amrikarisma/stm32f407xxx-mega-layout/firmware/speeduino/202501/speeduino.ini

;-------------------------------------------------------------------------------
#unset enablehardware_test

[MegaTune]
   MTversion      = 2.25

   queryCommand   = "Q"
   signature      = "speeduino 202501"
   versionInfo    = "S" ;This info is what is displayed to user

[TunerStudio]
   iniSpecVersion = 3.64

;-------------------------------------------------------------------------------

[SettingGroups]
   ; the referenceName will over-ride previous, so if you are creating a
   ; settingGroup with a reference name of lambdaSensor, it will replace the
   ; setting group defined in the settingGroups.xml of the TunerStudio config
   ; folder. If is is an undefined referenceName, it will be added.
   ; keyword    =  referenceName,  DisplayName

    ;settingGroup = boostUnits, "Boost table units"
    ;settingOption = DEFAULT, "kPa"
    ;settingOption = BOOSTPSI, "PSI"

    settingGroup = pressure_units, "Pressure Display"
    settingOption = DEFAULT, "PSI"
    settingOption = pressure_bar, "BAR"

    settingGroup = enablehardware_test, "Enable Hardware Test Page"

    settingGroup = resetcontrol_group, "Reset Control Features"
    settingOption = resetcontrol_standard, "Basic Options Only"
    settingOption = resetcontrol_adv, "Advanced Features (16u2 Firmware Update Required)"

    settingGroup  = mcu, "Controller in use"
    settingOption = DEFAULT, "Arduino Mega 2560"
    settingOption = mcu_teensy, "Teensy"
    settingOption = mcu_stm32, "STM32"

    settingGroup = COMMS_COMPAT_GROUP, "Serial Mode"
    settingOption = COMMS_COMPAT, "Compatibility Mode"
    settingOption = DEFAULT, "Normal"

    settingGroup = COMMS_MSDROID_COMPAT, "msDroid Compatibility-ONLY enable on Android"
    settingOption = MSDROID_COMPAT, "Enable"
    settingOption = DEFAULT, "Disable"

[PcVariables]
   ; valid types: boolean, double, int, list
   ;
   ; no offset as they are local variables.
   ; entry format the same as Constants, except there is no offset.
   ; arrays are not yet supported.
   ; name = class,  type,    shape,  units,       scale, translate,    lo,      hi, digits
   ; name = type, min, max;
   ;
   ; type List: value will be index.
    tsCanId          = bits,     U08,   [0:3], "CAN ID 0", "CAN ID 1", "CAN ID 2", "CAN ID 3", "CAN ID 4", "CAN ID 5", "CAN ID 6", "CAN ID 7", "CAN ID 8", "CAN ID 9", "CAN ID 10","CAN ID 11","CAN ID 12","CAN ID 13","CAN ID 14","INVALID"
    rpmhigh = scalar,   U16,    "rpm", 1, 0, 0, 30000, 0
    rpmwarn = scalar,   U16,    "rpm", 1, 0, 0, 30000, 0
    rpmdang = scalar,   U16,    "rpm", 1, 0, 0, 30000, 0
    maphigh = scalar,   U16,    "kPa", 1, 0, 0, 30000, 0
    mapwarn = scalar,   U16,    "kPa", 1, 0, 0, 30000, 0
    mapdang = scalar,   U16,    "kPa", 1, 0, 0, 30000, 0
    batlow  = scalar,   U08,    "Volts",  .1, 0, 0, 25.5,   1
    bathigh = scalar,   U08,    "Volts",  .1, 0, 0, 25.5,   1

#if LAMBDA
    wueAFR = array, S16,  [10], "Lambda", { 0.1 / stoich }, 0.000, -0.300, 0.300, 3
#else
    wueAFR = array, S16,  [10], "AFR", 0.1,   0.0, -4.0, 4.0, 1
#endif
    wueRecommended = array, U08,  [10], "%", 1.0,  0.0, 100, 255.0, 0

    idleUnits = bits,   U08,    [0:2], "None", "On/Off", "Duty Cycle", "Duty Cycle", "Steps", "Steps"

    boardFuelOutputs  = array,   U08,   [128],   " ", 1.0, 0, 0, 255, 0, noMsqSave
    boardIgnOutputs   = array,   U08,   [128],   " ", 1.0, 0, 0, 255, 0, noMsqSave
    boardHasRTC       = array,   U08,   [128],   " ", 1.0, 0, 0, 255, 0, noMsqSave

    ;These are used for padding out bits variables
    #define invalid_x8      = "INVALID", "INVALID", "INVALID", "INVALID", "INVALID", "INVALID", "INVALID", "INVALID"
    #define invalid_x16     = $invalid_x8,  $invalid_x8
    #define invalid_x24     = $invalid_x16, $invalid_x8
    #define invalid_x32     = $invalid_x16, $invalid_x16
    #define invalid_x64     = $invalid_x32, $invalid_x32
    #define invalid_x128    = $invalid_x64, $invalid_x64
    #define invalid_x256    = $invalid_x128, $invalid_x128
    #define invalid_x512    = $invalid_x256, $invalid_x256
    #define invalid_x1024   = $invalid_x512, $invalid_x512
    #define invalid_x2048   = $invalid_x1024, $invalid_x1024
    #define invalid_x4096   = $invalid_x2048, $invalid_x2048
    #define invalid_x8192   = $invalid_x4096, $invalid_x4096
    #define invalid_x16384  = $invalid_x8192, $invalid_x8192
    #define invalid_x32768  = $invalid_x16384, $invalid_x16384

    #define loadSourceNames = "MAP", "TPS", "IMAP/EMAP", "INVALID",   "INVALID", "INVALID", "INVALID", "INVALID"
    #define loadSourceUnits = "kPa",           "% TPS",   "%",         "INVALID", "INVALID", "INVALID", "INVALID", "INVALID"
    algorithmNames          = bits,    U08,   [0:2], $loadSourceNames
    algorithmUnits          = bits,    U08,   [0:2], "kPa",           "% TPS",   "%",         "% TPS", "INVALID", "INVALID", "INVALID", "INVALID"
    algorithmLimits         = array,   U16,   [8],   "", 1.0, 0, 0, 511, 0, noMsqSave
    fuel2SwitchUnits        = bits,    U08,   [0:2], "rpm", "kPa",          "% TPS",   "%",         "% TPS", "INVALID", "INVALID", "INVALID"

    ;All definitions of split fullStatus should keep 32 options
    #define fullStatus_def_1= "seconds", "status bits", "Engine status", "syncLossCounter", "MAP (Kpa)", "INVALID", "IAT / MAT", "coolant",  "batCorrection", "battery voltage x10", "O2", "egoCorrection", "iatCorrection", "wueCorrection", "RPM", "INVALID", "AEamount/2", "GammaE", "INVALID", "VE1", "VE2", "AFR Target", "TPS DOT", "INVALID", "Advance", "TPS", "loopsPerSecond", "INVALID", "free RAM", "INVALID", "boostTarget/2", "Boost duty"
    #define fullStatus_def_2= "spark bits", "RPM DOT", "INVALID", "ethanolPct", "flexCorrection", "flexIgnCorrection", "idle Load", "testOutputs", "O2_2", "baro", "Aux in 0", "INVALID", "Aux in 1", "INVALID", "Aux in 2", "INVALID", "Aux in 3", "INVALID", "Aux in 4", "INVALID", "Aux in 5", "INVALID", "Aux in 6", "INVALID", "Aux in 7", "INVALID", "Aux in 8", "INVALID", "Aux in 9", "INVALID", "Aux in 10", "INVALID"
    #define fullStatus_def_3= "Aux in 11", "INVALID", "Aux in 12", "INVALID", "Aux in 13", "INVALID", "Aux in 14", "INVALID", "Aux in 15", "INVALID", "TPS ADC", "Error code", "Pulsewidth 1", "INVALID", "Pulsewidth 2", "INVALID", "Pulsewidth 3", "INVALID", "Pulsewidth 4", "INVALID", "status bits 3", "engineProtectStatus", "Fuel load", "INVALID", "Ignition load", "INVALID", "dwell", "INVALID", "idle C.L. target", "MAP DOT", "INVALID", "VVT1 Angle"
    #define fullStatus_def_4= "INVALID", "VVT1 Target", "VVT1 duty", "flexBoostCorrection", "INVALID", "baro correction", "Current VE", "ASE Value", "vss", "INVALID", "Gear", "Fuel Pressure", "Oil Pressure", "WMI duty", "WMI empty", "VVT2 angle", "INVALID", "VVT2 target", "VVT2 duty", "outputs status", "Fuel temp", "Fuel temp correction", "Advance 1", "Advance 2", "SD status", "EMAP", "INVALID", "Fan duty", "airConStatus", "INVALID", "INVALID"
    #define fullStatus_def_5= $invalid_x32
    #define fullStatus_def_6= $invalid_x32
    #define fullStatus_def_7= $invalid_x32
    ;Rules start at index 240
    #define fullStatus_def_8= "INVALID", "INVALID", "INVALID", "INVALID", "INVALID", "INVALID", "INVALID", "INVALID", "INVALID", "INVALID", "INVALID", "INVALID", "INVALID", "INVALID", "INVALID", "INVALID", "running seconds x10", "Rule 1", "Rule 2", "Rule 3", "Rule 4", "Rule 5", "Rule 6", "Rule 7", "Rule 8", "INVALID", "INVALID", "INVALID", "INVALID", "INVALID", "INVALID", "INVALID", "INVALID"
    #define fullStatus_def  = $fullStatus_def_1, $fullStatus_def_2, $fullStatus_def_3, $fullStatus_def_4, $fullStatus_def_5, $fullStatus_def_6, $fullStatus_def_7, $fullStatus_def_8

    #define pinLayouts      = "INVALID", "Speeduino v0.2", "Speeduino v0.3", "Speeduino v0.4", "INVALID", "INVALID", "01-05 MX5 PNP", "INVALID", "96-97 MX5 PNP", "NA6 MX5 PNP", "Turtana PCB", "INVALID", "INVALID", "INVALID", "INVALID", "INVALID", "INVALID", "INVALID", "INVALID", "INVALID", "Plazomat I/O 0.1", "INVALID", "INVALID", "INVALID", "INVALID", "INVALID", "INVALID", "INVALID", "INVALID", "INVALID", "Daz V6 Shield 0.1", "BMW PnP", "INVALID", "INVALID", "INVALID", "INVALID", "INVALID", "INVALID", "INVALID", "INVALID", "NO2C", "UA4C", "BlitzboxBL49sp", "INVALID", "INVALID", "DIY-EFI CORE4 v1.0", "INVALID", "INVALID", "INVALID", "INVALID", "dvjcodec Teensy RevA", "dvjcodec Teensy RevB", "INVALID", "JUICEBOX", "INVALID", "Drop Bear", "INVALID", "INVALID", "INVALID", "INVALID", "Black STM32F407VET6 V0.1", "INVALID", "INVALID", "INVALID", "Mazduino Compact", $invalid_x128, $invalid_x64

    boostTableLabels    = bits,    U08,   [0:1], "Duty Cycle %", "kPa"
    boostByGearLabels   = bits,    U08,   [0:1], "", "%", "Limit", ""
    prgm_out_selection  = bits,    U08,   [0:2], "1", "2", "3", "4", "5", "6", "7", "8"

    fuelLoadMax     = scalar, U08, "", 1, 0, 0, 511, 0
    ignLoadMax      = scalar, U08, "", 1, 0, 0, 511, 0
    fuel2LoadMax    = scalar, U08, "", 1, 0, 0, 511, 0
    ign2LoadMax     = scalar, U08, "", 1, 0, 0, 511, 0
    AUXin00Alias    = string, ASCII, 20
    AUXin01Alias    = string, ASCII, 20 
    AUXin02Alias    = string, ASCII, 20 
    AUXin03Alias    = string, ASCII, 20 
    AUXin04Alias    = string, ASCII, 20 
    AUXin05Alias    = string, ASCII, 20 
    AUXin06Alias    = string, ASCII, 20 
    AUXin07Alias    = string, ASCII, 20 
    AUXin08Alias    = string, ASCII, 20 
    AUXin09Alias    = string, ASCII, 20 
    AUXin10Alias    = string, ASCII, 20 
    AUXin11Alias    = string, ASCII, 20 
    AUXin12Alias    = string, ASCII, 20 
    AUXin13Alias    = string, ASCII, 20 
    AUXin14Alias    = string, ASCII, 20 
    AUXin15Alias    = string, ASCII, 20

    prgm_out00Alias  = string, ASCII, 20
    prgm_out01Alias  = string, ASCII, 20 
    prgm_out02Alias  = string, ASCII, 20 
    prgm_out03Alias  = string, ASCII, 20 
    prgm_out04Alias  = string, ASCII, 20 
    prgm_out05Alias  = string, ASCII, 20 
    prgm_out06Alias  = string, ASCII, 20 
    prgm_out07Alias  = string, ASCII, 20 

    ;Define aliases for all the triggers. Naming pattern matches that used in decoders.ino
    #define trigger_missingTooth        = 0
    #define trigger_BasicDistributor    = 1
    #define trigger_DualWheel           = 2
    #define trigger_GM7X                = 3
    #define trigger_4G63                = 4
    #define trigger_24X                 = 5
    #define trigger_Jeep2000            = 6
    #define trigger_Audi135             = 7
    #define trigger_HondaD17            = 8
    #define trigger_Miata9905           = 9
    #define trigger_MazdaAU             = 10
    #define trigger_non360              = 11
    #define trigger_Nissan360           = 12
    #define trigger_Subaru67            = 13
    #define trigger_Daihatsu            = 14
    #define trigger_Harley              = 15
    #define trigger_ThirtySixMinus222   = 16
    #define trigger_ThirtySixMinus21    = 17
    #define trigger_420a                = 18
    #define trigger_Webber              = 19
    #define trigger_FordST170           = 20
    #define trigger_DRZ400              = 21
    #define trigger_NGC                 = 22
    #define trigger_VMAX                = 23
    #define trigger_renix               = 24
    #define trigger_Rover				        = 25
    #define trigger_K6A  				        = 26
    #define trigger_HondaJ32            = 27

[Constants]

   ;----------------------------------------------------------------------------
   ; Constants Definition
   ; --------------------
   ;
   ; Scalar Values
   ; -------------
   ; The scaling and translation values are used as follows:
   ;    msValue   = userValue / scale - translate
   ;    userValue = (msValue + translate) * scale
   ;
   ;
   ; Temperatures are fine, check out the Fielding IAC example (fastIdleT).
   ;
   ; Array Values
   ; ------------
   ; Arrays are specified just like scalars, except that they have a "shape"
   ; entry in the fourth parameter.  The shape allows you to define lists or
   ; tables, for example [8] defines a list with eight values and [2x4] defines
   ; a table with eight values (two rows and four columns).  Tables may be
   ; stored in either "X-" or "Y-order."  X-order means that memory is laid
   ; out like.
   ;
   ;     [x1,y1] [x2,y1]...[xn,y1] [x1,y2]...
   ;
   ; Y-order would be
   ;
   ;     [x1,y1] [x1,y2]...[x1,yn] [x2,y1]...
   ;
   ; To use the TableEditor, you must define two lists and a table, and
   ; the lengths of the lists must correspond to the shape of the table.
   ;
   ; Bit Fields
   ; ----------
   ; Bits are numbered 0-7, the rightmost being bit zero.  The basic
   ; data word that stores bit fields must be unsigned.
   ;
   ; You need NOT supply the correct number of labels matching the
   ; number of bits you've specified (one bit requires 2 values, two
   ; bits requires 4 values and so on).  If you neglect to supply enough
   ; labels, they will be synthesised using the sequence "1", "2" and so
   ; on based upon their position in the sequence (the cltType and matType
   ; will end up with identical lists).
   ;
   ; If you specify a label as "INVALID" (all upper case), then it will
   ; not be displayed in the combo box, so you can leave out values that
   ; make no sense.
   ;
   ;----------------------------------------------------------------------------

    endianness          = little
    nPages              = 15
    pageSize            = 128,   288,     288,    128,     288,    128,    240,     384,    192,    192,    288,    192,    128,    288,    256

    ; New commands
    pageIdentifier      = "\$tsCanId\x01", "\$tsCanId\x02", "\$tsCanId\x03", "\$tsCanId\x04", "\$tsCanId\x05", "\$tsCanId\x06", "\$tsCanId\x07", "\$tsCanId\x08", "\$tsCanId\x09", "\$tsCanId\x0A", "\$tsCanId\x0B", "\$tsCanId\x0C", "\$tsCanId\x0D", "\$tsCanId\x0E", "\$tsCanId\x0F"
    pageReadCommand     = "p%2i%2o%2c", "p%2i%2o%2c", "p%2i%2o%2c", "p%2i%2o%2c", "p%2i%2o%2c", "p%2i%2o%2c", "p%2i%2o%2c", "p%2i%2o%2c", "p%2i%2o%2c", "p%2i%2o%2c", "p%2i%2o%2c", "p%2i%2o%2c", "p%2i%2o%2c", "p%2i%2o%2c", "p%2i%2o%2c"
    pageValueWrite      = "M%2i%2o%2c%v", "M%2i%2o%2c%v", "M%2i%2o%2c%v", "M%2i%2o%2c%v", "M%2i%2o%2c%v", "M%2i%2o%2c%v", "M%2i%2o%2c%v", "M%2i%2o%2c%v", "M%2i%2o%2c%v", "M%2i%2o%2c%v", "M%2i%2o%2c%v", "M%2i%2o%2c%v", "M%2i%2o%2c%v", "M%2i%2o%2c%v", "M%2i%2o%2c%v"
    pageChunkWrite      = "M%2i%2o%2c%v", "M%2i%2o%2c%v", "M%2i%2o%2c%v", "M%2i%2o%2c%v", "M%2i%2o%2c%v", "M%2i%2o%2c%v", "M%2i%2o%2c%v", "M%2i%2o%2c%v", "M%2i%2o%2c%v", "M%2i%2o%2c%v", "M%2i%2o%2c%v", "M%2i%2o%2c%v", "M%2i%2o%2c%v", "M%2i%2o%2c%v", "M%2i%2o%2c%v"
    crc32CheckCommand   = "d%2i", "d%2i", "d%2i", "d%2i", "d%2i", "d%2i", "d%2i", "d%2i", "d%2i", "d%2i", "d%2i", "d%2i", "d%2i", "d%2i", "d%2i"
#if COMMS_COMPAT
    ;Comms compat mode uses a different burn command in order to slow down the EEPROM burn rate
    burnCommand         = "B%2i", "B%2i", "B%2i", "B%2i", "B%2i", "B%2i", "B%2i", "B%2i", "B%2i", "B%2i", "B%2i", "B%2i", "B%2i", "B%2i", "B%2i"
#else
    burnCommand         = "b%2i", "b%2i", "b%2i", "b%2i", "b%2i", "b%2i", "b%2i", "b%2i", "b%2i", "b%2i", "b%2i", "b%2i", "b%2i", "b%2i", "b%2i"
#endif


#if mcu_stm32
    blockingFactor = 121
#else
    blockingFactor = 251 ; Serial buffer is 257 bytes and there are 6 bytes of overhead (2 for the size and 4 for the CRC). Total payload is therefore 257-6=251.
#endif
#if COMMS_COMPAT
    blockingFactor = 121
#endif
    delayAfterPortOpen=1000
    ;validateArrayBounds = true
    blockReadTimeout = 2000
    tsWriteBlocks = on
    interWriteDelay = 10 ;Ignored when tsWriteBlocks is on
    pageActivationDelay = 10
    restrictSquirtRelationship = false ;This requires TS 3.1 or above
    #if MSDROID_COMPAT
      ;Do nothing
    #else
    messageEnvelopeFormat = msEnvelope_1.0 ;New and testing only
    tableCrcCommand     = "k\$tsCanId%2i%2o%2c" ;TS can only use this command in new mode
    #endif
    readSdCompressed = false

    ;New for TS 3.0.08ish upwards, define lists of standard I/O options

    #define ANALOG_PIN_MEGA       = "A0", "A1", "A2", "A3", "A4", "A5", "A6", "A7", "A8", "A9", "A10", "A11", "A12", "A13", "A14", "A15", $invalid_x32, $invalid_x16
    #define ANALOG_PIN_TEENSY     = "A0", "A1", "A2", "A3", "A4", "A5", "A6", "A7", "A8", "A9", "A10", "A11", "A12", "A13", "A14", "A15", "A16", "A17", "A18", "A19", "A20", "A21", "A22", "INVALID", $invalid_x24, $invalid_x16
    #define ANALOG_PIN_STM32      = "A0", "A1", "A2", "A3", "A4", "A5", "A6", "A7", "A8", "A9", "A10", "A11", "A12", "A13", "A14", "A15", $invalid_x32, $invalid_x16
    
    #define DIGITAL_PIN           = "Board Default", "INVALID", "INVALID", "3", "4", "5", "6", "7", "8", "9", "10", "11", "12", "13", "14", "15", "16", "17", "18", "19", "20", "21", "22", "23", "24", "25", "26", "27", "28", "29", "30", "31", "32", "33", "34", "35", "36", "37", "38", "39", "40", "41", "42", "43", "44", "45", "46", "47", "48", "49", "50", "51", "52", "53", "INVALID", "A8", "A9", "A10", "A11", "A12", "A13", "A14", "A15", "INVALID"
    #define IO_Pins_no_def        = "INVALID", "INVALID", "INVALID", "3", "4", "5", "6", "7", "8", "9", "10", "11", "12", "13", "14", "15", "16", "17", "18", "19", "20", "21", "22", "23", "24", "25", "26", "27", "28", "29", "30", "31", "32", "33", "34", "35", "36", "37", "38", "39", "40", "41", "42", "43", "44", "45", "46", "47", "48", "49", "50", "51", "52", "53", "INVALID", "A8", "A9", "A10", "A11", "A12", "A13", "A14", "A15", "INVALID"
    
    #define DIGITAL_AUX_PIN_MEGA      = "1", "2", "3", "4", "5", "6", "7", "8", "9", "10", "11", "12", "13", "14", "15", "16", "17", "18", "19", "20", "21", "22", "23", "24", "25", "26", "27", "28", "29", "30", "31", "32", "33", "34", "35", "36", "37", "38", "39", "40", "41", "42", "43", "44", "45", "46", "47", "48", "49", "50", "51", "52", "53", "INVALID", "INVALID", "INVALID", "INVALID", "INVALID", "INVALID", "INVALID", "INVALID", "INVALID", "INVALID", "INVALID"
    #define DIGITAL_AUX_PIN_TEENSY    = "1", "2", "3", "4", "5", "6", "7", "8", "9", "10", "11", "12", "13", "14", "15", "16", "17", "18", "19", "20", "21", "22", "23", "24", "25", "26", "27", "28", "29", "30", "31", "32", "33", "34", "35", "36", "37", "38", "39", "40", "41", "42", "43", "44", "45", "46", "47", "48", "49", "50", "51", "52", "53", "INVALID", "INVALID", "INVALID", "INVALID", "INVALID", "INVALID", "INVALID", "INVALID", "INVALID", "INVALID", "INVALID"
    #define DIGITAL_AUX_PIN_STM32     = "1", "2", "3", "4", "5", "6", "7", "8", "9", "10", "11", "12", "13", "14", "15", "16", "17", "18", "19", "20", "21", "22", "23", "24", "25", "26", "27", "28", "29", "30", "31", "32", "33", "34", "35", "36", "37", "38", "39", "40", "41", "42", "43", "44", "45", "46", "47", "48", "49", "50", "51", "52", "53", "INVALID", "INVALID", "INVALID", "INVALID", "INVALID", "INVALID", "INVALID", "INVALID", "INVALID", "INVALID", "INVALID"

    ;Pins and defs used for aux out comparison functions
    #define bitwise_def     = "Disabled",  "AND",  "OR",  "XOR"
    #define comparator_def  = "== (equal)",  "!= (different)",  "> (greater)",  ">= (greater/equal)",  "< (smaller)",  "<= (smaller/equal)",  "& (and)",  "^ (xor)"
    #define comp_IO_Pins_0  = "Disabled", "INVALID", "INVALID", "3", "4", "5", "6", "7", "8", "9", "10", "11", "12", "13", "14", "15", "16", "17", "18", "19", "20", "21", "22", "23", "24", "25", "26", "27", "28", "29", "30", "31", "32", "33", "34", "35", "36", "37", "38", "39", "40", "41", "42", "43", "44", "45", "46", "47", "48", "49", "50", "51", "52", "53", "INVALID", "A8", "A9", "A10", "A11", "A12", "A13", "A14", "A15", "INVALID"
    #define comp_IO_Pins_1  = $invalid_x32
    #define comp_IO_Pins_2  = $invalid_x32
    #define comp_IO_Pins_3  = "Virtual", "INVALID", "INVALID", "INVALID", "INVALID", "INVALID", "INVALID", "INVALID", $invalid_x64, $invalid_x32, $invalid_x16, $invalid_x8
    #define comp_IO_Pins    = $comp_IO_Pins_0, $comp_IO_Pins_1, $comp_IO_Pins_2, $comp_IO_Pins_3

    #define tsCanId_list          = "CAN ID 0", "CAN ID 1", "CAN ID 2", "CAN ID 3", "CAN ID 4", "CAN ID 5", "CAN ID 6", "CAN ID 7", "CAN ID 8", "CAN ID 9", "CAN ID 10","CAN ID 11","CAN ID 12","CAN ID 13","CAN ID 14","INVALID"
    #define CAN_ADDRESS_HEX_00XX  = "INVALID", "0x001", "0x002", "0x003", "0x004", "0x005", "0x006", "0x007", "0x008", "0x009", "0x00A", "0x00B", "0x00C", "0x00D", "0x00E", "0x00F", "0x010", "0x011", "0x012", "0x013", "0x014", "0x015", "0x016", "0x017", "0x018", "0x019", "0x01A", "0x01B", "0x01C", "0x01D", "0x01E", "0x01F", "0x020", "0x021", "0x022", "0x023", "0x024", "0x025", "0x026", "0x027", "0x028", "0x029", "0x02A", "0x02B", "0x02C", "0x02D", "0x02E", "0x02F", "0x030", "0x031", "0x032", "0x033", "0x034", "0x035", "0x036", "0x037", "0x038", "0x039", "0x03A", "0x03B", "0x03C", "0x03D", "0x03E", "0x03F", "0x040", "0x041", "0x042", "0x043", "0x044", "0x045", "0x046", "0x047", "0x048", "0x049", "0x04A", "0x04B", "0x04C", "0x04D", "0x04E", "0x04F", "0x050", "0x051", "0x052", "0x053", "0x054", "0x055", "0x056", "0x057", "0x058", "0x059", "0x05A", "0x05B", "0x05C", "0x05D", "0x05E", "0x05F" ,"0x060", "0x061", "0x062", "0x063", "0x064", "0x065", "0x066", "0x067", "0x068", "0x069", "0x06A", "0x06B", "0x06C", "0x06D", "0x06E", "0x06F", "0x070", "0x071", "0x072", "0x073", "0x074", "0x075", "0x076", "0x077", "0x078", "0x079", "0x07A", "0x07B", "0x07C", "0x07D", "0x07E", "0x07F", "0x080", "0x081", "0x082", "0x083", "0x084", "0x085", "0x086", "0x087", "0x088", "0x089", "0x08A", "0x08B", "0x08C", "0x08D", "0x08E", "0x08F" ,"0x090", "0x091", "0x092", "0x093", "0x094", "0x095", "0x096", "0x097", "0x098", "0x099", "0x09A", "0x09B", "0x09C", "0x09D", "0x09E", "0x09F", "0x0A0", "0x0A1", "0x0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
    #define CAN_ADDRESS_HEX       =  $CAN_ADDRESS_HEX_01XX, $CAN_ADDRESS_HEX_02XX, $CAN_ADDRESS_HEX_03XX, $CAN_ADDRESS_HEX_04XX, $CAN_ADDRESS_HEX_05XX, $CAN_ADDRESS_HEX_06XX, $CAN_ADDRESS_HEX_07XX, $invalid_x32768, $invalid_x16384, $invalid_x8192, $invalid_x4096, $invalid_x2048, $invalid_x256

;--------------------------------------------------
;Start Page 1
;Page 1 is all general settings. Note that some of these (algorithm and ignAlgorithm) MUST come before their use in the bitStringValue() calls in the fuel and ignition tables
;--------------------------------------------------
page = 1
      aseTaperTime  = scalar, U08,       0,         "S",        0.1,       0.0,   0.0,    25.5,      1
      aeColdPct     = scalar, U08,       1,         "%",      1.0,       0,   100,    255,       0 ;AE cold adjustment %
#if CELSIUS
      aeColdTaperMin= scalar, U08,       2,       "C", 1.0,       -40,    -40,    215,      0     ;AE cold adjustment, taper start clt (full adjustment)
#else
      aeColdTaperMin= scalar, U08,       2,       "F", 1.8,    -22.23,    -40,    419,      0     ;AE cold adjustment, taper start clt (full adjustment)
#endif
    
      aeMode        = bits,   U08,       3, [0:1],  "TPS", "MAP", "INVALID", "INVALID"
      battVCorMode  = bits,   U08,       3, [2:2],  "Whole PW", "Open Time only"
      SoftLimitMode = bits,   U08,       3, [3:3],  "Fixed", "Relative "
      useTachoSweep = bits,   U08,       3, [4:4],  "Off", "On"
      aeApplyMode   = bits,   U08,       3, [5:5],  "PW Multiplier", "PW Adder"
      multiplyMAP   = bits,   U08,       3, [6:7],  "Off", "Baro", "Fixed", "INVALID"
      wueRates      = array,  U08,       4, [10],   "%",        1.0,       0.0,   0.0,    255,       0
      crankingPct   = scalar, U08,      14,         "%",        1.0,       0.0,   0.0,    255,       0
      pinLayout     = bits,   U08,      15, [0:7],  $pinLayouts
      tachoPin      = bits,   U08,      16, [0:5],  "Board Default", "1", "2", "3", "4", "5", "6", "7", "8", "9", "10", "11", "12", "13", "14", "15", "16", "17", "18", "19", "20", "21", "22", "23", "24", "25", "26", "27", "28", "29", "30", "31", "32", "33", "34", "35", "36", "37", "38", "39", "40", "41", "42", "43", "44", "45", "46", "47", "48", "49", "50", "51", "52", "53", "INVALID", "INVALID", "INVALID", "INVALID", "INVALID", "INVALID", "INVALID", "INVALID", "INVALID", "INVALID"
      tachoDiv      = bits,   U08,      16, [6:7],  "Normal", "Half", "INVALID", "INVALID"
      tachoDuration = scalar, U08,      17,         "ms",       1.0,       0.0,   1.0,    6.0,       0
      maeThresh     = scalar, U08,      18,         "kPa/s",    1.0,       0.0,   0.0,    255,       0 ;MAP threshold for triggering AE
      taeThresh     = scalar, U08,      19,         "%/s",      1.0,       0.0,   0.0,    255,       0 ;TPS threshold for triggering AE
      aeTime        = scalar, U08,      20,         "ms",        10,       0.0,   0.0,    2550,      0
      taeMinChange  = scalar, U08,      21,         "%",        0.5,         0,     0,    5.0,       1
      maeMinChange  = scalar, U08,      22,         "kPa",      1.0,         0,     0,    10.0,      0

      ; Display (Options for what the display is showing)
      displayB1     = bits,   U08,      23, [0:3],  "RPM", "PW", "Advance", "VE", "GammaE", "TPS", "IAT", "CLT"
      displayB2     = bits,   U08,      23, [4:7],  "RPM", "PW", "Advance", "VE", "GammaE", "TPS", "IAT", "CLT"

      reqFuel       = scalar, U08,      24,        "ms",        0.1,       0.0,   0.0,    25.5,      1
      divider       = scalar, U08,      25,        "",          1.0,       0.0
      alternate     = bits,   U08,      26, [0:0], "Simultaneous", "Alternating"
      crkngAddCLTAdv= bits,   U08,      26, [1:1], "No",       "Yes"
      includeAFR    = bits,   U08,      26, [2:2], "No",       "Yes"
      hardCutType   = bits,   U08,      26, [3:3], "Full",      "Rolling"
      ignAlgorithm  = bits,   U08,      26, [4:6], $loadSourceNames
      indInjAng     = bits,   U08,      26, [7:7], "Disabled", "Enabled"
      injOpen       = scalar, U08,      27,        "ms",        0.1,       0.0,   0.1,    25.5,      1
      injAng        = array,  U16,      28, [4],   "deg",       1.0,       0.0,   0.0,    720,       0

      ; Config1
      mapSample     = bits,   U08,      36, [0:1], "Instantaneous", "Cycle Average", "Cycle Minimum", "Event Average"
      twoStroke     = bits,   U08,      36, [2:2], "Four-stroke", "Two-stroke"
      injType       = bits,   U08,      36, [3:3], "Port", "Throttle Body"
      nCylinders    = bits,   U08,      36, [4:7], "INVALID","1","2","3","4","5","6","INVALID","8","INVALID","INVALID","INVALID","INVALID","INVALID","INVALID","INVALID"

      ; Config2
      algorithm     = bits,   U08,      37, [0:2], $loadSourceNames ;Has to be called algorithm for the req fuel calculator to work :(
      fixAngEnable  = bits,   U08,      37, [3:3], "Off", "On"
      nInjectors    = bits,   U08,      37, [4:7], "INVALID","1","2","3","4","5","6","INVALID","8","INVALID","INVALID","INVALID","INVALID","INVALID","INVALID","INVALID"

      ; Config3
      engineType    = bits,   U08,      38, [0:0], "Even fire",     "Odd fire"
      flexEnabled   = bits,   U08,      38, [1:1], "Off", "On"
      legacyMAP     = bits,   U08,      38, [2:2], "No", "Yes" ;Whether to use the older legacy MAP reading that had the pullup enabled
      baroCorr      = bits,   U08,      38, [3:3], "Off",           "On"
      injLayout     = bits,   U08,      38, [4:5], "Paired", "Semi-Sequential", "INVALID", "Sequential"
      perToothIgn   = bits,   U08,      38, [6:6], "No", "Yes"
      dfcoEnabled   = bits,   U08,      38, [7:7], "Off",       "On"

#if CELSIUS
      aeColdTaperMax = scalar, U08,       39,       "C", 1.0,       -40,    -40,    215,      0     ;AE cold adjustment, taper start clt (full adjustment)
#else
      aeColdTaperMax = scalar, U08,       39,       "F", 1.8,    -22.23,    -40,    419,      0     ;AE cold adjustment, taper end clt (no adjustment)
#endif

      dutyLim       = scalar, U08,      40,        "%",         1.0,       0.0,   0.0,     95.0,     0
      flexFreqLow   = scalar, U08,      41,        "Hz",        1.0,       0.0,   0.0,     250.0,    0
      flexFreqHigh  = scalar, U08,      42,        "Hz",        1.0,       0.0,   0.0,     250.0,    0

      boostMaxDuty  = scalar, U08,      43,        "%",         1.0,       0.0,   0.0,     100.0,    0
      tpsMin        = scalar, U08,      44,        "ADC",       1.0,       0.0,   0.0,     255.0,    0
      tpsMax        = scalar, U08,      45,        "ADC",       1.0,       0.0,   0.0,     255.0,    0
      mapMin        = scalar, S08,      46,        "kpa",       1.0,       0.0,  -100,     127.0,    0
      mapMax        = scalar, U16,      47,        "kpa",       1.0,       0.0,   0.0,     25500,    0
      fpPrime       = scalar, U08,      49,        "s",         1.0,       0.0,   0.0,     255.0,    0
      stoich        = scalar, U08,      50,        ":1",        0.1,       0.0,   0.0,     25.5,     1
      oddfire2      = scalar, U16,      51,        "deg",       1.0,       0.0,   0.0,     720,      0 ; * (  2 byte)
      oddfire3      = scalar, U16,      53,        "deg",       1.0,       0.0,   0.0,     720,      0 ; * (  2 byte)
      oddfire4      = scalar, U16,      55,        "deg",       1.0,       0.0,   0.0,     720,      0 ; * (  2 byte)

      idleUpPin     = bits,   U08,      57, [0:5], "Board Default", "INVALID", "INVALID", "3", "4", "5", "6", "7", "8", "9", "10", "11", "12", "13", "14", "15", "16", "17", "18", "19", "20", "21", "22", "23", "24", "25", "26", "27", "28", "29", "30", "31", "32", "33", "34", "35", "36", "37", "38", "39", "40", "41", "42", "43", "44", "45", "46", "47", "48", "49", "50", "51", "52", "53", "INVALID", "A8", "A9", "A10", "A11", "A12", "A13", "A14", "A15", "INVALID"
      idleUpPolarity= bits,   U08,      57, [6:6], "Normal", "Inverted"
      idleUpEnabled = bits,   U08,      57, [7:7], "Off", "On"
      idleUpAdder   = scalar, U08,      58,        "% / Steps",  1.0,       0.0,   0.0,     250.0,    0
      aeTaperMin    = scalar, U08,      59,        "RPM",       100,       0.0,   1000,    10000,    0
      aeTaperMax    = scalar, U08,      60,        "RPM",       100,       0.0,   2000,    10000,    0

      iacCLminValue = scalar, U08,      61,       "% / Steps", {idleRes},   0.0,   0.0, {idleResMax},    0 ; Minimum and maximum duty cycles when using closed loop idle
      iacCLmaxValue = scalar, U08,      62,       "% / Steps", {idleRes},   0.0,   0.0, {idleResMax},    0
      boostMinDuty  = scalar, U08,      63,        "%",         1.0,       0.0,   0.0,     100.0,    0 ; Minimum and maximum duty cycles for boost control

      baroMin       = scalar, S08,      64,        "kpa",       1.0,       0.0,  -100,     127.0,    0
      baroMax       = scalar, U16,      65,        "kpa",       1.0,       0.0,   0.0,     25500,    0
      EMAPMin       = scalar, S08,      67,        "kpa",       1.0,       0.0,  -100,     127.0,    0
      EMAPMax       = scalar, U16,      68,        "kpa",       1.0,       0.0,   0.0,     25500,    0

      fanWhenOff      = bits,   U08,    70, [0:0], "No",        "Yes" 
      fanWhenCranking = bits,   U08,    70, [1:1], "No",        "Yes" 
      useDwellMap     = bits,   U08,    70, [2:2], "No",        "Yes" 
      fanEnable       = bits,   U08,    70, [3:4], "Off",       "On/Off",  "PWM",  "INVALID"
      rtc_mode        = bits,   U08,    70, [5:6], "Off", "On-board", "INVALID", "INVALID"
      incorporateAFR  = bits,   U08,    70, [7:7], "No",        "Yes"

      asePct        = array,  U08,       71, [4],    "%",        1.0,       0.0,     0,    155,       0
      aseCount      = array,  U08,       75, [4],    "s",     1.0,       0.0,     0.0,     255,    0 ; Values for the afterstart enrichment curve
#if CELSIUS
      aseBins       = array,  U08,       79, [4],  "C", 1.0,       -40,    -40,    215,      0
#else
      aseBins       = array,  U08,       79, [4],  "F", 1.8,    -22.23,    -40,    419,      0
#endif
      primePulse    = array,  U08,       83, [4],  "ms",        0.5,       0.0,   0.0,     127.5,     1
#if CELSIUS
      primeBins     = array,  U08,       87, [4],  "C", 1.0,       -40,    -40,    215,      0
#else
      primeBins     = array,  U08,       87, [4],  "F", 1.8,    -22.23,    -40,    419,      0
#endif
      CTPSPin       = bits,  U08,  91, [0:5], "Board Default", "INVALID", "INVALID", "3", "4", "5", "6", "7", "8", "9", "10", "11", "12", "13", "14", "15", "16", "17", "18", "19", "20", "21", "22", "23", "24", "25", "26", "27", "28", "29", "30", "31", "32", "33", "34", "35", "36", "37", "38", "39", "40", "41", "42", "43", "44", "45", "46", "47", "48", "49", "50", "51", "52", "53", "INVALID", "A8", "A9", "A10", "A11", "A12", "A13", "A14", "A15", "INVALID"
      CTPSPolarity  = bits,  U08,  91, [6:6], "Normal", "Inverted"
      CTPSEnabled   = bits,  U08,  91, [7:7], "Off", "On"
      idleAdvEnabled      = bits,  U08,  92, [0:1], "Off", "Added", "Switched", "INVALID"
      idleAdvAlgorithm    = bits,  U08,  92, [2:2], "TPS", "CTPS"
      ;idleAdvDelay        = bits,  U08,  92, [3:7], "0", "1", "2", "3", "4", "5", "6", "7", "8", "9", "10", "11", "12", "13", "14", "15", "16", "17", "18", "19", "20", "21", "22", "23", "24", "25", "26", "27", "28", "29", "INVALID", "INVALID"
      idleAdvDelay        = bits,  U08,  92, [3:7], "0.0", "0.5", "1.0", "1.5", "2.0", "2.5", "3.0", "3.5", "4.0", "4.5", "5.0", "5.5", "6.0", "6.5", "7.0", "7.5", "8.0", "8.5", "9.0", "9.5", "10.0", "10.5", "11.0", "11.5", "12.0", "12.5", "13.0", "13.5", "14.0", "14.5", "INVALID", "INVALID"
      idleAdvRPM   = scalar,  U08,      93,       "rpm",        100,       0.0,   100,   25500,      0
      idleAdvTPS   = scalar,  U08,      94,         "%",        0.5,         0,     0,   100.0,      1

      injAngRPM     = array,  U08,      95, [4],   "RPM",        100,       0.0,   100,    10000,    0
      idleTaperTime = scalar, U08,      99,    "S",         0.1,       0.0,   0.0,    25.5,      1
      dfcoDelay     = scalar, U08,      100,   "S",         0.1,       0.0,   0.0,    25.5,      1 ;Remainder of DFCO settings are in page 4
#if CELSIUS
      dfcoMinCLT    = scalar,  U08,      101,    "C", 1.0,       -40,    -40,    215,      0
#else
      dfcoMinCLT    = scalar,  U08,      101,    "F", 1.8,    -22.23,    -40,    419,      0
#endif

      ;VSS settings
      vssMode       = bits,  U08,         102, [0:1], "Off", "CAN/Serial/Analog", "Pulses per KM", "Pulses per mile"
      ;vssPullup     = bits,  U08,       102, [1:1], "Off", "On"
      vssPin        = bits,  U08,       102, [2:7], "Board Default", "INVALID", "INVALID", "3", "4", "5", "6", "7", "8", "9", "10", "11", "12", "13", "14", "15", "16", "17", "18", "19", "20", "21", "22", "23", "24", "25", "26", "27", "28", "29", "30", "31", "32", "33", "34", "35", "36", "37", "38", "39", "40", "41", "42", "43", "44", "45", "46", "47", "48", "49", "50", "51", "52", "53", "INVALID", "A8", "A9", "A10", "A11", "A12", "A13", "A14", "A15", "INVALID"
      vssPulsesPerKm= scalar, U16,      103,        "pulses",     1.0,       0.0,   0.0,     25500,    0
      vssSmoothing  = scalar, U08,      105,         "%",        1.0,         0,     0,     255,      0
      vssRatio1     = scalar, U16,      106, "km/h per 1000rpm", 0.1,         0,     0,     99.9,     1
      vssRatio2     = scalar, U16,      108, "km/h per 1000rpm", 0.1,         0,     0,     99.9,     1
      vssRatio3     = scalar, U16,      110, "km/h per 1000rpm", 0.1,         0,     0,     99.9,     1
      vssRatio4     = scalar, U16,      112, "km/h per 1000rpm", 0.1,         0,     0,     99.9,     1
      vssRatio5     = scalar, U16,      114, "km/h per 1000rpm", 0.1,         0,     0,     99.9,     1
      vssRatio6     = scalar, U16,      116, "km/h per 1000rpm", 0.1,         0,     0,     99.9,     1
    
      ;Idle up output (AC Fan) settings
      idleUpOutputEnabled   = bits,   U08,      118, [0:0], "Off", "On"
      idleUpOutputInv       = bits,   U08,      118, [1:1], "No", "Yes"
      idleUpOutputPin       = bits,   U08,      118, [2:7], "Board Default", "INVALID", "INVALID", "3", "4", "5", "6", "7", "8", "9", "10", "11", "12", "13", "14", "15", "16", "17", "18", "19", "20", "21", "22", "23", "24", "25", "26", "27", "28", "29", "30", "31", "32", "33", "34", "35", "36", "37", "38", "39", "40", "41", "42", "43", "44", "45", "46", "47", "48", "49", "50", "51", "52", "53", "INVALID", "A8", "A9", "A10", "A11", "A12", "A13", "A14", "A15", "INVALID"
      
      tachoSweepMaxRPM  = scalar,   U08,        119,        "RPM", 100,       0.0,   100,    10000,    0
      primingDelay      = scalar,   U08,        120,        "S",   0.1,       0.0,   0.0,     25.5,      1
      
      iacTPSlimit               = scalar, U08,  121,        "%",  0.5,         0,     0,    100.0,     1
      iacRPMlimitHysteresis     = scalar, U08,  122,      "RPM",   10,         0,    10,     2500,     0

      rtc_trim        = scalar,  S08,    123,               "ppm",      1, 0, -127, +127, 0
      idleAdvVss      = scalar, U08,      124,        "km/h",       1,       0.0,   0.0,     255,      0 
      mapSwitchPoint  = scalar, U08,      125,        "RPM",      100,       0.0,   0.0,     16320,    0

      unused0_126               = bits,   U08,  126, [0:2]
      ;These are reserved for future use, in case of more CAN broadcasting features are added
      canWBO                    = bits,   U08,  126, [2:3], "Off", "rusEFI WBO", "AEM", "INVALID"
      vssAuxCh                  = bits,   U08,  126, [4:7], "Aux0", "Aux1", "Aux2", "Aux3", "Aux4", "Aux5", "Aux6", "Aux7", "Aux8", "Aux9", "Aux10", "Aux11", "Aux12", "Aux13", "Aux14", "Aux15"
      decelAmount               = scalar, U08,  127,        "%",  1.0,       0.0,   0.0,     150.0,    0

;Page 2 is the fuel map and axis bins only
page = 2
   ;  name       = bits,   type,    offset, bits
   ;  name       = array,  type,    offset, shape, units,     scale, translate,    lo,      hi, digits
   ;  name       = scalar, type,    offset,        units,     scale, translate,    lo,      hi, digits
      veTable    = array,  U08,       0, [16x16],"%",          1.0,      0.0,   0.0,   255.0,      0
      rpmBins    = array,  U08,     256, [  16], "RPM",      100.0,      0.0,   100.0, 25500.0,      0
      fuelLoadBins = array,  U08,   272, [  16], { bitStringValue(algorithmUnits ,  algorithm) },       {fuelLoadRes},      0.0,   0.0,   {fuelLoadMax},      {fuelDecimalRes}
      ;fuelLoadBins = array,  U08,   272, [  16], { bitStringValue(algorithmUnits ,  algorithm) },        2.0,      0.0,   0.0,   { arrayValue(rpmBins , algorithm) },      0

;--------------------------------------------------
;Start Ignition table (Page 3)
;--------------------------------------------------
page = 3
      advTable1   = array,  U08,     0,[16x16],  "deg",       1.0,       -40,   -40,   70.0,      0
      rpmBins2    = array,  U08,   256,[   16],  "RPM",       100.0,     0.0,   100,   25500,      0
      mapBins1    = array,  U08,   272, [  16], { bitStringValue(algorithmUnits ,  ignAlgorithm) },     {ignLoadRes},      0.0,   0.0,   {ignLoadMax},      {ignDecimalRes} ; This name has to be used in order for the table to show up in MLVs table. I can't find the regexs that make this work :(

;--------------------------------------------------
;Start Page 4
;These are primarily ignition related settings (Previously part of page 2)
;--------------------------------------------------
page = 4
      TrigAng    = scalar, S16,      0,         "Deg",       1,        0,     -360,     360,        0
      FixAng     = scalar, S08,      2,         "Deg",       1,        0,     -64,      64,         0 ; Allow negative values here
      CrankAng   = scalar, S08,      3,         "Deg",       1,        0,     -10,      80,         0
      TrigAngMul = scalar, U08,      4,         "",          1,        0,     0,        88,         0 ; Multiplier for tooth counts that don't evenly divide into 360
      TrigEdge   = bits,   U08,      5,[0:0],    "RISING", "FALLING"
      TrigSpeed  = bits,   U08,      5,[1:1],    "Crank Speed", "Cam Speed"
      IgInv      = bits,   U08,      5,[2:2],    "Going Low",        "Going High"
      TrigPattern= bits,   U08,      5,[3:7],    "Missing Tooth", "Basic Distributor", "Dual Wheel", "GM 7X", "4G63 / Miata / 3000GT", "GM 24X", "Jeep 2000", "Audi 135", "Honda D17", "Miata 99-05", "Mazda AU", "Non-360 Dual", "Nissan 360", "Subaru 6/7", "Daihatsu +1", "Harley EVO", "36-2-2-2", "36-2-1", "DSM 420a", "Weber-Marelli", "Ford ST170", "DRZ400", "Chrysler NGC", "Yamaha Vmax 1990+", "Renix", "Rover MEMS", "K6A", "Honda J32", "INVALID", "INVALID", "INVALID", "INVALID"
      TrigEdgeSec= bits,   U08,      6,[0:0],    "RISING", "FALLING"
      fuelPumpPin= bits  , U08,      6,[1:6],    "Board Default", "INVALID", "INVALID", "3", "4", "5", "6", "7", "8", "9", "10", "11", "12", "13", "14", "15", "16", "17", "18", "19", "20", "21", "22", "23", "24", "25", "26", "27", "28", "29", "30", "31", "32", "33", "34", "35", "36", "37", "38", "39", "40", "41", "42", "43", "44", "45", "46", "47", "48", "49", "50", "51", "52", "53", "INVALID", "A8", "A9", "A10", "A11", "A12", "A13", "A14", "A15", "INVALID"
      useResync  = bits,   U08,      6,[7:7],    "No",        "Yes"
      sparkDur   = scalar, U08,      7,          "ms",        0.1, 0, 0, 25.5, 1 ; Spark duration
      trigPatternSec = bits,U08,     8,[0:6],    "Single tooth cam", "4-1 cam", "Poll level", "Rover 5-3-2 cam", "Toyota 3 Tooth", "INVALID", "INVALID", "INVALID", "INVALID", "INVALID", "INVALID", "INVALID", "INVALID", "INVALID", "INVALID", "INVALID", "INVALID", "INVALID", "INVALID", "INVALID", "INVALID", "INVALID", "INVALID", "INVALID", "INVALID", "INVALID", "INVALID", "INVALID", "INVALID", "INVALID", "INVALID", "INVALID", "INVALID", "INVALID", "INVALID", "INVALID", "INVALID", "INVALID", "INVALID", "INVALID", "INVALID", "INVALID", "INVALID", "INVALID", "INVALID", "INVALID", "INVALID", "INVALID", "INVALID", "INVALID", "INVALID", "INVALID", "INVALID", "INVALID", "INVALID", "INVALID", "INVALID", "INVALID", "INVALID", "INVALID", "INVALID", "INVALID", "INVALID", "INVALID", "INVALID", "INVALID", "INVALID", "INVALID", "INVALID", "INVALID", "INVALID", "INVALID", "INVALID", "INVALID", "INVALID", "INVALID", "INVALID", "INVALID", "INVALID", "INVALID", "INVALID", "INVALID", "INVALID", "INVALID", "INVALID", "INVALID", "INVALID", "INVALID", "INVALID", "INVALID", "INVALID", "INVALID", "INVALID", "INVALID", "INVALID", "INVALID", "INVALID", "INVALID", "INVALID", "INVALID", "INVALID", "INVALID", "INVALID", "INVALID", "INVALID", "INVALID", "INVALID", "INVALID", "INVALID", "INVALID", "INVALID", "INVALID", "INVALID", "INVALID", "INVALID", "INVALID", "INVALID", "INVALID", "INVALID", "INVALID", "INVALID", "INVALID", "INVALID", "INVALID", "INVALID", "INVALID", "INVALID", "INVALID"
      PollLevelPol = bits, U08,      8,[7:7],    "Low", "High",

;Reset Control
      bootloaderCaps  = scalar, U08, 9,        "level",    1, 0, 0, 255, 0
#if resetcontrol_adv
      resetControl =    bits,   U08, 10,[0:1], "Disabled", "Prevent When Running", "Prevent Always", "Serial Command"
#else
      resetControl =    bits,   U08, 10,[0:1], "Disabled", "INVALID", "INVALID", "Serial Command"
#endif
      resetControlPin = bits,   U08, 10,[2:7],  "Board Default", "INVALID", "INVALID", "3", "4", "5", "6", "7", "8", "9", "10", "11", "12", "13", "14", "15", "16", "17", "18", "19", "20", "21", "22", "23", "24", "25", "26", "27", "28", "29", "30", "31", "32", "33", "34", "35", "36", "37", "38", "39", "40", "41", "42", "43", "44", "45", "46", "47", "48", "49", "50", "51", "52", "53", "INVALID", "A8", "A9", "A10", "A11", "A12", "A13", "A14", "A15", "INVALID"

      SkipCycles  = scalar, U08,     11,         "cycles",    1,    0,    0,  255, 0

   ;  name       = array,  type,    offset, shape, units,     scale, translate,    lo,      hi, digits
   ;  name       = scalar, type,    offset,      units,     scale, translate,    lo,      hi, digits
;Dwell control
      boostType     = bits,   U08,     12, [0:0],  "Open Loop",  "Closed Loop"
      useDwellLim   = bits,   U08,     12, [1:1],   "Off",    "On"
      sparkMode     = bits,   U08,     12, [2:4],  "Wasted Spark", "Single Channel",   "Wasted COP", "Sequential", "Rotary", "INVALID", "INVALID", "INVALID"
      TrigFilter    = bits,   U08,     12, [5:6],  "Off", "Weak", "Medium", "Aggressive"
      ignCranklock  = bits,   U08,     12, [7:7],  "Off",  "On"
      dwellcrank    = scalar, U08,     13,         "ms",       0.1,    0,    0, 25, 1
      dwellrun      = scalar, U08,     14,         "ms",       0.1,    0,    0, 8, 1 ;running dwell variable railed to 8 - who needs more than 8ms?
      numTeeth      = scalar, U08,     15,         "teeth",    1.0,    0.0,  0.0,     255,       0
      missingTeeth  = scalar, U08,     16,         "teeth",    1.0,    0.0,  0.0,     255,       0

      crankRPM      = scalar, U08,     17,         "rpm",      10,    0.0,  100, 1000, 0
      tpsflood      = scalar, U08,     18,         "%",        0.5,    0.0,  0.0,   100.0,      1

;Rev Limits
      SoftRevLim    = scalar, U08,  19,         "rpm",      100,    0.0,  100, 25500, 0
      SoftLimRetard = scalar, U08,  20,         "deg",      1.0,    0.0,  0.0,   80,   0
      SoftLimMax    = scalar, U08,  21,         "s",        0.1,    0.0,  0.0,  25.5,   1
      hardRevLim    = scalar, U08,  22,         "rpm",      100,    0.0, 100, 25500,  0

;TPS based acceleration enrichment
      taeBins    = array,  U08,     23, [ 4],   "%/s",      10.0,   0.0,  0.00,   2550.0,      0
      taeRates   = array,  U08,     27, [ 4],   "%",        1.0,    0.0,  0.00,    255.0,      0 ; 4 bytes
;WUE Bins (Needed somewhere to put these
    #if CELSIUS
      wueBins    = array,  U08,     31, [10],   "C",        1.0, -40,  -40,  102.0,      0
    #else
      wueBins    = array,  U08,     31, [10],   "F",        1.8,   -22.23,  -40,  215.0,      0
    #endif
;Dwell config options
      dwellLim   = scalar, U08,     41,         "ms",       1,      0,        0, 32, 0
      dwellRates = array,  U08,     42, [6],    "%",        1.0,    0.0,      0.00,   255.0,      0

;IAT (Inlet air temp) timing retard
    #if CELSIUS
      iatRetBins   = array,  U08,     48, [ 6],   "C",      1.0,    0.0,  0.00,   125.0,      0
    #else
      iatRetBins   = array,  U08,     48, [ 6],   "F",      1.8,    17.77,  32.00,   257.0,      0 ; No -40 degree offset here
    #endif
      iatRetRates  = array,  U08,     54, [ 6],   "deg",    1.0,    0.0,  0.00,   30.0,      0
;Deceleration Fuel Cut Off (DFCO)
      dfcoRPM      = scalar, U08,      60,        "RPM",      10.0,  0.0,   100,     2550,    0
      dfcoHyster   = scalar, U08,      61,        "RPM",      2.0,  0.0,   100,     500.0,    0
      dfcoTPSThresh= scalar, U08,      62,        "%",        0.5,  0.0,     0,     100.0,    1
;Cranking ignition bypass
      ignBypassEnable = bits,   U08,  63, [0:0],      "Off",        "On"
      ignBypassPin    = bits,   U08,  63, [1:6],      "INVALID", "INVALID", "INVALID", "3", "4", "5", "6", "7", "8", "9", "10", "11", "12", "13", "14", "15", "16", "17", "18", "19", "20", "21", "22", "23", "24", "25", "26", "27", "28", "29", "30", "31", "32", "33", "34", "35", "36", "37", "38", "39", "40", "41", "42", "43", "44", "45", "46", "47", "48", "49", "50", "51", "52", "53", "INVALID", "INVALID", "INVALID", "INVALID", "INVALID", "INVALID", "INVALID", "INVALID", "INVALID", "INVALID"
      ignBypassHiLo   = bits,   U08,  63, [7:7],      "LOW",        "HIGH"
;Analog input filter levels (Note max values are 240 so that default values of 255 can be overwritten on bootup)
      ADCFILTER_TPS   = scalar, U08,      64, "%",          1.0,  0.0,   0,     240,    0
      ADCFILTER_CLT   = scalar, U08,      65, "%",          1.0,  0.0,   0,     240,    0
      ADCFILTER_IAT   = scalar, U08,      66, "%",          1.0,  0.0,   0,     240,    0
      ADCFILTER_O2    = scalar, U08,      67, "%",          1.0,  0.0,   0,     240,    0
      ADCFILTER_BAT   = scalar, U08,      68, "%",          1.0,  0.0,   0,     240,    0
      ADCFILTER_MAP   = scalar, U08,      69, "%",          1.0,  0.0,   0,     240,    0
      ADCFILTER_BARO  = scalar, U08,      70, "%",          1.0,  0.0,   0,     240,    0

;CLT (Coolant temp) timing Advance/Retard
    #if CELSIUS
      cltAdvBins   = array,  U08,     71, [ 6],   "C",      1.0,    -40,  -40,   102.0,      0
    #else
      cltAdvBins   = array,  U08,     71, [ 6],   "F",      1.8,    -22.23,  -40,   215.0,      0 ; No -40 degree offset here
    #endif
      cltAdvValues    = array,  S08,     77, [ 6],   "deg",    1.0,     -15,  -15,   15,      0

;MAP based acceleration enrichment
      maeBins         = array,  U08,      83, [ 4],   "kpa/s",    10.0,   0.0,  0.00,   2550.0,      0
      maeRates        = array,  U08,      87, [ 4],   "%",        1.0,    0.0,  0.00, 255.0,      0 ; 4 bytes

      batVoltCorrect  = scalar, S08,      91, "v",          0.1,  0.0,    -2,     2,        1 ;Battery reading calibration value. Note: Signed value

;Baro fuel correction
      baroFuelBins    = array,  U08,      92, [8],    "kPa",  1.0,    0,  70, 120,        0 ; Bins for the Baro correction curve
      baroFuelValues  = array,  U08,     100, [8],     "%",   1.0,    0,  0,  255,        0 ; % Values for same

;Idle timing advance
      idleAdvBins     = array,  U08,      108, [6],    "RPM",    10.0,      -50,       -500,     500,         0
      idleAdvValues   = array,  U08,      114, [6],    "deg",     1.0,      -15,        -15,      50,         0

      engineProtectMaxRPM   = scalar, U08,  120,         "rpm",      100,    0.0, 100, 25500,  0

      vvt2CL0DutyAng  = scalar, S16,      121,         "deg",    1.0,   0.0,  -360.0,  360.0,      0 ; * (  2 bytes)
      vvt2PWMdir      = bits,   U08,      123, [0:0],  "Advance", "Retard"
      inj4CylPairing  = bits,   U08,      123, [1:2],  "1+3 & 2+4", "1+4 & 2+3", "INVALID", "INVALID"
      dwellErrCorrect = bits,   U08,      123, [3:3],  "Off", "On"
      CANBroadcastProt= bits,   U08,      123, [4:6],  "Off", "BMW", "VAG", "Haltech", "INVALID", "INVALID", "INVALID", "INVALID"
      unusedBits4_123 = bits,   U08,      123, [7:7]
      ANGLEFILTER_VVT = scalar, U08,      124, "%",          1.0,  0.0,   0,     100,    0
      FILTER_FLEX     = scalar, U08,      125, "%",          1.0,  0.0,   0,     240,    0

      #if CELSIUS
      vvtMinClt       = scalar,  U08,      126, "C",        1.0,    -40,    -40,    215,      0     
      #else
      vvtMinClt       = scalar,  U08,      126, "F",        1.8,    -22.23,    -40,    419,      0
      #endif
      vvtDelay        = scalar,  U08,      127, "S",        5.0,  0.0,   0,     1275,    0

;--------------------------------------------------

;Start AFR page
;--------------------------------------------------
page = 5
      lambdaTable = array,  U08,              0, [16x16], "Lambda",  { 0.1 / stoich },   0.0000,  0.00,    2.00,      3
      afrTable    = array,  U08,     lastOffset, [16x16],    "AFR",               0.1,      0.0,     7,    25.5,      1

      rpmBinsAFR  = array,  U08,   256,[   16],    "RPM",   100.0,     0.0,   100,   25500,      0
      loadBinsAFR  = array,  U08,   272,[   16],    { bitStringValue(algorithmUnits ,  algorithm) },   {fuelLoadRes},      0.0,   0.0,   {fuelLoadMax},      {fuelDecimalRes}

;--------------------------------------------------
;Start page 6
; Page 6 is all settings associated with O2/AFR
;--------------------------------------------------
page = 6
      egoAlgorithm            = bits  , U08,       0,      [0:1], "Simple", "INVALID", "PID", "No correction" ; * (  1 byte)
      egoType                 = bits  , U08,       0,      [2:3], "Disabled", "Narrow Band", "Wide Band", "INVALID"                  ; egoOption
      boostEnabled            = bits,   U08,       0,      [4:4], "Off", "On"
      vvtEnabled              = bits,   U08,       0,      [5:5], "Off", "On"
      engineProtectType       = bits,   U08,       0,      [6:7], "Off", "Spark Only", "Fuel Only","Both"

      egoKP                   = scalar, U08,       1,             "%",        1.0,   0.0,  0.0,  200.0,      0 ; * (  1 byte)
      egoKI                   = scalar, U08,       2,             "%",        1.0,   0.0,  0.0,  200.0,      0 ; * (  1 byte)
      egoKD                   = scalar, U08,       3,             "%",        1.0,   0.0,  0.0,  200.0,      0 ; * (  1 byte)
  #if CELSIUS
      egoTemp                 = scalar, U08,        4,             "C",        1.0, -40,  -40,  102.0,      0
  #else
      egoTemp                 = scalar, U08,        4,             "F",       1.8,   -22.23,  -40,  419.0,      0
  #endif
      egoCount                = scalar, U08,       5,             "",         4.0,    0.0,  4.0,  255.0,      0 ; * (  1 byte)
      vvtMode                 = bits,   U08,       6, [0:1],      "On/Off", "Open Loop", "Closed loop", "INVALID"
      vvtLoadSource           = bits,   U08,       6, [2:3],      "MAP", "TPS", "INVALID", "INVALID"
      vvtPWMdir               = bits,   U08,       6, [4:4],      "Advance", "Retard"
      vvtCLUseHold            = bits,   U08,       6, [5:5],      "No", "Yes"
      vvtCLAlterFuelTiming    = bits,   U08,       6, [6:6],      "No", "Yes"
      boostCutEnabled         = bits,   U08,       6, [7:7],      "Off", "On"
      egoLimit                = scalar, U08,       7,             "",         1,      0,    0,    16,         0
      
      ego_min_afr    = scalar, U08,          8,    "AFR",  0.1          , 0,  7          ,  25          , 1
      ego_min_lambda = scalar, U08, lastOffset, "Lambda", {0.1 / stoich}, 0, {7 / stoich}, {25 / stoich}, 3
      ego_max_afr    = scalar, U08,          9,    "AFR",  0.1          , 0,  7          ,  25          , 1
      ego_max_lambda = scalar, U08, lastOffset, "Lambda", {0.1 / stoich}, 0, {7 / stoich}, {25 / stoich}, 3

      ego_sdelay  = scalar, U08,      10,             "sec",      1,      0,    0,    120,        0
      egoRPM      = scalar, U08,      11,             "rpm",      100,    0.0,  100,  25500,      0
      egoTPSMax   = scalar, U08,      12,             "%",        0.5,      0,    0,  100.0,      1
      vvt1Pin      = bits  , U08,      13, [0:5],      "Board Default", "INVALID", "INVALID", "3", "4", "5", "6", "7", "8", "9", "10", "11", "12", "13", "14", "15", "16", "17", "18", "19", "20", "21", "22", "23", "24", "25", "26", "27", "28", "29", "30", "31", "32", "33", "34", "35", "36", "37", "38", "39", "40", "41", "42", "43", "44", "45", "46", "47", "48", "49", "50", "51", "52", "53", "INVALID", "INVALID", "INVALID", "INVALID", "INVALID", "INVALID", "INVALID", "INVALID", "INVALID", "INVALID"
      useExtBaro  =   bits, U08,      13, [6:6],      "No", "Yes"
      boostMode   =   bits, U08,      13, [7:7],      "Simple", "Full"
      boostPin    =   bits, U08,      14, [0:5],      "Board Default", "INVALID", "INVALID", "3", "4", "5", "6", "7", "8", "9", "10", "11", "12", "13", "14", "15", "16", "17", "18", "19", "20", "21", "22", "23", "24", "25", "26", "27", "28", "29", "30", "31", "32", "33", "34", "35", "36", "37", "38", "39", "40", "41", "42", "43", "44", "45", "46", "47", "48", "49", "50", "51", "52", "53", "INVALID", "INVALID", "INVALID", "INVALID", "INVALID", "INVALID", "INVALID", "INVALID", "INVALID", "INVALID"
      tachoMode   =   bits, U08,      14, [6:6],      "Fixed Duration", "Match Dwell"
      useEMAP     =   bits, U08,      14, [7:7],      "No", "Yes"
      brvBins     = array,  U08,      15, [6],        "V",        0.1,    0,    6,    24,         1 ; Bins for the battery reference voltage
      injBatRates = array,  U08,      21, [6],        "%",        1,      0,    0,    255,        0 ;Values for injector pulsewidth vs voltage
  #if CELSIUS
      airDenBins  = array,  U08,      27, [9],        "C",        1.0,    -40,  -40,  215,        0 ; Bins for the air density correction curve
  #else
      airDenBins  = array,  U08,      27, [9],        "F",        1.8,    -22.23,  -40,  419,        0 ; Bins for the air density correction curve
  #endif
      airDenRates = array,  U08,      36, [9],        "%",        1.0,    0.0,  0,    255,        0 ; Values for the air density correction curve

; PWM Frequencies
      boostFreq   = scalar, U08,      45,             "Hz",       2.0,    0.0,  10,   511,        0
      vvtFreq     = scalar, U08,      46,             "Hz",       2.0,    0.0,  10,   511,        0
      idleFreq    = scalar, U08,      47,             "Hz",       2.0,    0.0,  10,   511,        0

; Launch Control
      launchPin   = bits  , U08,      48, [0:5],      "Board Default", "INVALID", "INVALID", "3", "4", "5", "6", "7", "8", "9", "10", "11", "12", "13", "14", "15", "16", "17", "18", "19", "20", "21", "22", "23", "24", "25", "26", "27", "28", "29", "30", "31", "32", "33", "34", "35", "36", "37", "38", "39", "40", "41", "42", "43", "44", "45", "46", "47", "48", "49", "50", "51", "52", "53", "INVALID", "INVALID", "INVALID", "INVALID", "INVALID", "INVALID", "INVALID", "INVALID", "INVALID", "INVALID"
      launchEnable= bits,   U08,      48, [6:6],      "No",        "Yes"
      launchHiLo  = bits,   U08,      48, [7:7],    "LOW",        "HIGH"

      lnchSoftLim = scalar, U08,      49,             "rpm",      100,    0.0,    100, 25500, 0
      lnchRetard  = scalar, S08,      50,             "deg",      1.0,    0.0,    -30,   40,   0
      lnchHardLim = scalar, U08,      51,             "rpm",      100,    0.0,    100, 25500,  0
      lnchFuelAdd = scalar, U08,      52,             "%",        1.0,    0.0,    0.0,   80,   0

      idleKP       = scalar, U08,     53,             "%",        0.03125,   0.0,  0.0,  7.96,      2 ; * (  1 byte)
      idleKI       = scalar, U08,     54,             "%",        0.03125,   0.0,  0.0,  7.96,      2 ; * (  1 byte)
      idleKD       = scalar, U08,     55,             "%",        0.00781,   0.0,  0.0,  1.99,      3 ; * (  1 byte)
      boostLimit   = scalar, U08,     56,             "kPa",      2.0,   0.0,  0.0,  511.0,      0
      boostKP      = scalar, U08,     57,             "%",        1.0,   0.0,  0.0,  200.0,      0 ; * (  1 byte)
      boostKI      = scalar, U08,     58,             "%",        1.0,   0.0,  0.0,  200.0,      0 ; * (  1 byte)
      boostKD      = scalar, U08,     59,             "%",        1.0,   0.0,  0.0,  200.0,      0 ; * (  1 byte)

      lnchPullRes  =   bits, U08,      60,        [0:0],      "Float"  , "Pullup"
      iacPWMrun    =   bits, U08,      60,        [1:1],      "No",        "Yes"
      fuelTrimEnabled= bits, U08,      60,        [2:2],      "No",        "Yes"
      flatSEnable  =   bits, U08,      60,        [3:3],      "No",        "Yes"
; Baro Sensor pin
      baroPin      =   bits, U08,      60,        [4:7],      "A0", "A1", "A2", "A3", "A4", "A5", "A6", "A7", "A8", "A9", "A10", "A11", "A12", "A13", "A14", "A15"

; Flat shift
      flatSSoftWin = scalar, U08,      61,             "rpm",      100,    0.0,  100, 25500,  0
      flatSRetard  = scalar, S08,      62,             "deg",      1.0,    0.0,-30.0,   80,   0
      flatSArm     = scalar, U08,      63,             "rpm",      100,    0.0,  100, 25500,  0

      iacCLValues  = array, U08,       64, [10],        "RPM",    10.0,  0.0,      0,  2550,     0
      iacOLStepVal = array, U08,       74, [10],       "Steps",      3,    0,      0,    765,    0
      iacOLPWMVal  = array, U08,       84, [10],       "Duty %",   1.0,    0,      0,      100,    0
  #if CELSIUS
      iacBins      = array, U08,       94, [10],       "C",        1.0,    -40,    -40,    215,      0
  #else
      iacBins      = array, U08,       94, [10],       "F",        1.8,    -22.23,    -40,    419,      0
  #endif
      iacCrankSteps= array, U08,      104, [4],        "Steps",      3,    0,    0,    765,    0
      iacCrankDuty = array, U08,      108, [4],        "Duty %",   1.0,    0,  0,  100,    0
  #if CELSIUS
      iacCrankBins = array, U08,      112, [4],        "C",        1.0,    -40,    -40,    215,      0
  #else
      iacCrankBins = array, U08,      112, [4],        "F",        1.8,    -22.23,    -40,    419,      0
  #endif

      iacAlgorithm = bits , U08,      116, [0:2],      "None", "On/Off", "PWM Open loop", "PWM Closed loop", "Stepper Open Loop", "Stepper Closed Loop", "PWM Closed+Open loop", "Stepper Closed+Open loop"
      iacStepTime  = bits , U08,      116, [3:5],      "INVALID","1", "2", "3", "4", "5", "6","INVALID"
      iacChannels  = bits,  U08,      116, [6:6],      "1", "2"
      iacPWMdir    = bits , U08,      116, [7:7],      "Normal", "Reverse"

  #if CELSIUS
      iacFastTemp  = scalar, U08,     117,             "C",        1.0,    -40,    -40,    215,      0
  #else
      iacFastTemp  = scalar, U08,     117,             "F",        1.8,    -22.23,    -40,    419,      0
  #endif

      iacStepHome  = scalar, U08,     118,             "Steps",         3,    0,    0, 765,   0
      iacStepHyster= scalar, U08,     119,             "Steps",         1,  0,  1.0,  10,   0

      ; Begin fan control variables
      fanInv       = bits,   U08,     120, [0:0], "No",        "Yes"
      fanUnused    = bits,   U08,     120, [1:1], "Off",       "On/Off"
      fanPin       = bits,   U08,     120, [2:7], "Board Default", "INVALID", "INVALID", "3", "4", "5", "6", "7", "8", "9", "10", "11", "12", "13", "14", "15", "16", "17", "18", "19", "20", "21", "22", "23", "24", "25", "26", "27", "28", "29", "30", "31", "32", "33", "34", "35", "36", "37", "38", "39", "40", "41", "42", "43", "44", "45", "46", "47", "48", "49", "50", "51", "52", "53", "INVALID", "A8", "A9", "A10", "A11", "A12", "A13", "A14", "A15", "INVALID"
  #if CELSIUS
      fanSP        = scalar, U08,     121,        "C",        1.0,       -40,     -40,     215.0,    0
      fanHyster    = scalar, U08,     122,        "C",        1.0,       0.0,  0.0,     40,    0
  #else
      fanSP        = scalar, U08,     121,        "F",        1.8,       -22.23,  -40,     419.0,    0
      fanHyster    = scalar, U08,     122,        "F",        1.0,       0.0,  0.0,     40,    0
  #endif
      fanFreq      = scalar, U08 ,    123,        "Hz",        2.0,        0.0,    10,     511,       0
  #if CELSIUS
      fanPWMBins = array, U08,      124, [4],        "C",        1.0,    -40,    -40,    215,      0
  #else
      fanPWMBins = array, U08,      124, [4],        "F",        1.8,    -22.23,    -40,    419,      0
  #endif

;--------------------------------------------------
;Boost and vvt maps (Page 7)
;--------------------------------------------------
page = 7
      boostTable    = array,  U08,    0,[8x8],    { bitStringValue( boostTableLabels, boostType ) },        2.0,        0.0,   0,       {boostTableLimit},      0
      rpmBinsBoost  = array,  U08,    64,[  8],   "RPM",      100.0,      0.0,   100,     25500,      0
      tpsBinsBoost  = array,  U08,    72,[  8],   "TPS",      0.5,        0.0,   0.0,     127.0,      1
      vvtTable      = array,  U08,    80,[8x8],    "%",        0.5,        0.0,   0,       100,      1
      rpmBinsVVT    = array,  U08,    144,[  8],   "RPM",      100.0,      0.0,   100,     25500,      0
      loadBinsVVT   = array,  U08,    152,[  8],   { bitStringValue(algorithmUnits ,  vvtLoadSource) },  {vvtLoadRes},        0.0,   0.0,     {vvtLoadMax},      {vvtDecimalRes}
;Fuel staging Table
      stagingTable  = array,  U08,    160, [8x8], "%",          1.0,      0.0,   0.0,   100.0,      0
      rpmBinsStaging= array,  U08,    224, [  8], "RPM",      100.0,      0.0,   100.0, 25500.0,      0
      loadBinsStaging= array,  U08,    232, [  8], { bitStringValue(algorithmUnits ,  algorithm) },   {fuelLoadRes},      0.0,   0.0,   {fuelLoadMax},      {fuelDecimalRes}

;--------------------------------------------------
;Sequential fuel trim tables (Page 8)
;--------------------------------------------------
page = 8
      fuelTrim1Table      = array,  U08,     0,[6x6],     "%",    1.0,    -128,   -50,    50,        0
      fuelTrim1rpmBins    = array,  U08,    36,[  6],     "RPM",  100.0,  0.0,   0,     25500,      0
      fuelTrim1loadBins   = array,  U08,    42,[  6],     { bitStringValue(algorithmUnits ,  algorithm) }, {fuelLoadRes},      0.0,   0.0,   {fuelLoadMax},      {fuelDecimalRes}

      fuelTrim2Table      = array,  U08,    48,[6x6],     "%",    1.0,    -128,   -50,    50,         0
      fuelTrim2rpmBins    = array,  U08,    84,[  6],     "RPM",  100.0,  0.0,   0,     25500,      0
      fuelTrim2loadBins   = array,  U08,    90,[  6],     { bitStringValue(algorithmUnits ,  algorithm) }, {fuelLoadRes},      0.0,   0.0,   {fuelLoadMax},      {fuelDecimalRes}

      fuelTrim3Table      = array,  U08,    96,[6x6],     "%",    1.0,    -128,  -50,     50,         0
      fuelTrim3rpmBins    = array,  U08,   132,[  6],     "RPM",  100.0,  0.0,   0,     25500,      0
      fuelTrim3loadBins   = array,  U08,   138,[  6],     { bitStringValue(algorithmUnits ,  algorithm) }, {fuelLoadRes},      0.0,   0.0,   {fuelLoadMax},      {fuelDecimalRes}

      fuelTrim4Table      = array,  U08,   144,[6x6],     "%",    1.0,    -128,  -50,     50,         0
      fuelTrim4rpmBins    = array,  U08,   180,[  6],     "RPM",  100.0,  0.0,   0,     25500,      0
      fuelTrim4loadBins   = array,  U08,   186,[  6],     { bitStringValue(algorithmUnits ,  algorithm) }, {fuelLoadRes},      0.0,   0.0,   {fuelLoadMax},      {fuelDecimalRes}

      fuelTrim5Table      = array,  U08,   192,[6x6],     "%",    1.0,    -128,   -50,    50,        0
      fuelTrim5rpmBins    = array,  U08,   228,[  6],     "RPM",  100.0,  0.0,   0,     25500,      0
      fuelTrim5loadBins   = array,  U08,   234,[  6],     { bitStringValue(algorithmUnits ,  algorithm) }, {fuelLoadRes},      0.0,   0.0,   {fuelLoadMax},      {fuelDecimalRes}

      fuelTrim6Table      = array,  U08,   240,[6x6],     "%",    1.0,    -128,   -50,    50,         0
      fuelTrim6rpmBins    = array,  U08,   276,[  6],     "RPM",  100.0,  0.0,   0,     25500,      0
      fuelTrim6loadBins   = array,  U08,   282,[  6],     { bitStringValue(algorithmUnits ,  algorithm) }, {fuelLoadRes},      0.0,   0.0,   {fuelLoadMax},      {fuelDecimalRes}

      fuelTrim7Table      = array,  U08,   288,[6x6],     "%",    1.0,    -128,  -50,     50,         0
      fuelTrim7rpmBins    = array,  U08,   324,[  6],     "RPM",  100.0,  0.0,   0,     25500,      0
      fuelTrim7loadBins   = array,  U08,   330,[  6],     { bitStringValue(algorithmUnits ,  algorithm) }, {fuelLoadRes},      0.0,   0.0,   {fuelLoadMax},      {fuelDecimalRes}

      fuelTrim8Table      = array,  U08,   336,[6x6],     "%",    1.0,    -128,  -50,     50,         0
      fuelTrim8rpmBins    = array,  U08,   372,[  6],     "RPM",  100.0,  0.0,   0,     25500,      0
      fuelTrim8loadBins   = array,  U08,   378,[  6],     { bitStringValue(algorithmUnits ,  algorithm) }, {fuelLoadRes},      0.0,   0.0,   {fuelLoadMax},      {fuelDecimalRes}

;--------------------------------------------------
;CANBUS control and Axillary IO(Page 9)
;--------------------------------------------------
page = 9
      enable_secondarySerial    = bits,   U08,     0, [0:0], "Disable", "Enable"
      intcan_available          = bits,   U08,     0, [1:1], "Disable", "Enable"
      enable_intcan             = bits,   U08,     0, [2:2], "Disable", "Enable"
      secondarySerialProtocol   = bits,   U08,     0, [3:6], "Generic (Fixed List)". "Generic (ini File)". "CAN", "msDroid", "Real Dash", "Tuner Studio", "INVALID", "INVALID", "INVALID", "INVALID", "INVALID", "INVALID", "INVALID", "INVALID", "INVALID", "INVALID"
    
      caninput_sel0a            = bits,   U08,     1, [0:1], "Off", "INVALID", "Analog_local", "Digital_local"
      caninput_sel0b            = bits,   U08,     1, [2:3], "Off", "External Source", "Analog_local", "Digital_local"
      caninput_sel0extsourcea   = bits,   U08,     1, [5:5], "Via Secondary Serial", "INVALID"
      caninput_sel0extsourceb   = bits,   U08,     1, [6:6], "Via Secondary Serial", "Via Internal CAN"        
      caninput_sel0extsourcec   = bits,   U08,     1, [7:7], "INVALID", "Via Internal CAN"

      caninput_sel1a            = bits,   U08,     2, [0:1], "Off", "INVALID", "Analog_local", "Digital_local"
      caninput_sel1b            = bits,   U08,     2, [2:3], "Off", "External Source", "Analog_local", "Digital_local"
      caninput_sel1extsourcea   = bits,   U08,     2, [5:5], "Via Secondary Serial", "INVALID"
      caninput_sel1extsourceb   = bits,   U08,     2, [6:6], "Via Secondary Serial", "Via Internal CAN"       
      caninput_sel1extsourcec   = bits,   U08,     2, [7:7], "INVALID", "Via Internal CAN"    

      caninput_sel2a            = bits,   U08,     3, [0:1], "Off", "INVALID", "Analog_local", "Digital_local"
      caninput_sel2b            = bits,   U08,     3, [2:3], "Off", "External Source", "Analog_local", "Digital_local"
      caninput_sel2extsourcea   = bits,   U08,     3, [5:5], "Via Secondary Serial", "INVALID"
      caninput_sel2extsourceb   = bits,   U08,     3, [6:6], "Via Secondary Serial", "Via Internal CAN"
      caninput_sel2extsourcec   = bits,   U08,     3, [7:7], "INVALID", "Via Internal CAN"    

      caninput_sel3a            = bits,   U08,     4, [0:1], "Off", "INVALID", "Analog_local", "Digital_local"
      caninput_sel3b            = bits,   U08,     4, [2:3], "Off", "External Source", "Analog_local", "Digital_local"
      caninput_sel3extsourcea   = bits,   U08,     4, [5:5], "Via Secondary Serial", "INVALID"
      caninput_sel3extsourceb   = bits,   U08,     4, [6:6], "Via Secondary Serial", "Via Internal CAN"
      caninput_sel3extsourcec   = bits,   U08,     4, [7:7], "INVALID", "Via Internal CAN"    

      caninput_sel4a            = bits,   U08,     5, [0:1], "Off", "INVALID", "Analog_local", "Digital_local"
      caninput_sel4b            = bits,   U08,     5, [2:3], "Off", "External Source", "Analog_local", "Digital_local"
      caninput_sel4extsourcea   = bits,   U08,     5, [5:5], "Via Secondary Serial", "INVALID"
      caninput_sel4extsourceb   = bits,   U08,     5, [6:6], "Via Secondary Serial", "Via Internal CAN"
      caninput_sel4extsourcec   = bits,   U08,     5, [7:7], "INVALID", "Via Internal CAN"    

      caninput_sel5a            = bits,   U08,     6, [0:1], "Off", "INVALID", "Analog_local", "Digital_local"
      caninput_sel5b            = bits,   U08,     6, [2:3], "Off", "External Source", "Analog_local", "Digital_local"
      caninput_sel5extsourcea   = bits,   U08,     6, [5:5], "Via Secondary Serial", "INVALID"
      caninput_sel5extsourceb   = bits,   U08,     6, [6:6], "Via Secondary Serial", "Via Internal CAN"
      caninput_sel5extsourcec   = bits,   U08,     6, [7:7], "INVALID", "Via Internal CAN"        

      caninput_sel6a            = bits,   U08,     7, [0:1], "Off", "INVALID", "Analog_local", "Digital_local"
      caninput_sel6b            = bits,   U08,     7, [2:3], "Off", "External Source", "Analog_local", "Digital_local"
      caninput_sel6extsourcea   = bits,   U08,     7, [5:5], "Via Secondary Serial", "INVALID"
      caninput_sel6extsourceb   = bits,   U08,     7, [6:6], "Via Secondary Serial", "Via Internal CAN"
      caninput_sel6extsourcec   = bits,   U08,     7, [7:7], "INVALID", "Via Internal CAN"    

      caninput_sel7a            = bits,   U08,     8, [0:1], "Off", "INVALID", "Analog_local", "Digital_local"
      caninput_sel7b            = bits,   U08,     8, [2:3], "Off", "External Source", "Analog_local", "Digital_local"
      caninput_sel7extsourcea   = bits,   U08,     8, [5:5], "Via Secondary Serial", "INVALID"
      caninput_sel7extsourceb   = bits,   U08,     8, [6:6], "Via Secondary Serial", "Via Internal CAN"
      caninput_sel7extsourcec   = bits,   U08,     8, [7:7], "INVALID", "Via Internal CAN"    

      caninput_sel8a            = bits,   U08,     9, [0:1], "Off", "INVALID", "Analog_local", "Digital_local"
      caninput_sel8b            = bits,   U08,     9, [2:3], "Off", "External Source", "Analog_local", "Digital_local"
      caninput_sel8extsourcea   = bits,   U08,     9, [5:5], "Via Secondary Serial", "INVALID"
      caninput_sel8extsourceb   = bits,   U08,     9, [6:6], "Via Secondary Serial", "Via Internal CAN"
      caninput_sel8extsourcec   = bits,   U08,     9, [7:7], "INVALID", "Via Internal CAN"    

      caninput_sel9a            = bits,   U08,     10, [0:1], "Off", "INVALID", "Analog_local", "Digital_local"
      caninput_sel9b            = bits,   U08,     10, [2:3], "Off", "External Source", "Analog_local", "Digital_local"
      caninput_sel9extsourcea   = bits,   U08,     10, [5:5], "Via Secondary Serial", "INVALID"
      caninput_sel9extsourceb   = bits,   U08,     10, [6:6], "Via Secondary Serial", "Via Internal CAN"
      caninput_sel9extsourcec   = bits,   U08,     10, [7:7], "INVALID", "Via Internal CAN"    
  
      caninput_sel10a           = bits,   U08,     11, [0:1], "Off", "INVALID", "Analog_local", "Digital_local"
      caninput_sel10b           = bits,   U08,     11, [2:3], "Off", "External Source", "Analog_local", "Digital_local"
      caninput_sel10extsourcea  = bits,   U08,     11, [5:5], "Via Secondary Serial", "INVALID"
      caninput_sel10extsourceb  = bits,   U08,     11, [6:6], "Via Secondary Serial", "Via Internal CAN"
      caninput_sel10extsourcec  = bits,   U08,     11, [7:7], "INVALID", "Via Internal CAN"    

      caninput_sel11a           = bits,   U08,     12, [0:1], "Off", "INVALID", "Analog_local", "Digital_local"
      caninput_sel11b           = bits,   U08,     12, [2:3], "Off", "External Source", "Analog_local", "Digital_local"
      caninput_sel11extsourcea  = bits,   U08,     12, [5:5], "Via Secondary Serial", "INVALID"
      caninput_sel11extsourceb  = bits,   U08,     12, [6:6], "Via Secondary Serial", "Via Internal CAN"
      caninput_sel11extsourcec  = bits,   U08,     12, [7:7], "INVALID", "Via Internal CAN"    

      caninput_sel12a           = bits,   U08,     13, [0:1], "Off", "INVALID", "Analog_local", "Digital_local"
      caninput_sel12b           = bits,   U08,     13, [2:3], "Off", "External Source", "Analog_local", "Digital_local"
      caninput_sel12extsourcea  = bits,   U08,     13, [5:5], "Via Secondary Serial", "INVALID"
      caninput_sel12extsourceb  = bits,   U08,     13, [6:6], "Via Secondary Serial", "Via Internal CAN"
      caninput_sel12extsourcec  = bits,   U08,     13, [7:7], "INVALID", "Via Internal CAN"    

      caninput_sel13a           = bits,   U08,     14, [0:1], "Off", "INVALID", "Analog_local", "Digital_local"
      caninput_sel13b           = bits,   U08,     14, [2:3], "Off", "External Source", "Analog_local", "Digital_local"
      caninput_sel13extsourcea  = bits,   U08,     14, [5:5], "Via Secondary Serial", "INVALID"
      caninput_sel13extsourceb  = bits,   U08,     14, [6:6], "Via Secondary Serial", "Via Internal CAN"
      caninput_sel13extsourcec  = bits,   U08,     14, [7:7], "INVALID", "Via Internal CAN"    

      caninput_sel14a           = bits,   U08,     15, [0:1], "Off", "INVALID", "Analog_local", "Digital_local"
      caninput_sel14b           = bits,   U08,     15, [2:3], "Off", "External Source", "Analog_local", "Digital_local"
      caninput_sel14extsourcea  = bits,   U08,     15, [5:5], "Via Secondary Serial", "INVALID"
      caninput_sel14extsourceb  = bits,   U08,     15, [6:6], "Via Secondary Serial", "Via Internal CAN"
      caninput_sel14extsourcec  = bits,   U08,     15, [7:7], "INVALID", "Via Internal CAN"    

      caninput_sel15a           = bits,   U08,     16, [0:1], "Off", "INVALID", "Analog_local", "Digital_local"
      caninput_sel15b           = bits,   U08,     16, [2:3], "Off", "External Source", "Analog_local", "Digital_local"
      caninput_sel15extsourcea  = bits,   U08,     16, [5:5], "Via Secondary Serial", "INVALID"
      caninput_sel15extsourceb  = bits,   U08,     16, [6:6], "Via Secondary Serial", "Via Internal CAN"
      caninput_sel15extsourcec  = bits,   U08,     16, [7:7], "INVALID", "Via Internal CAN"    
          
      caninput_source_can_address0 = bits,   U16,     17,         [0:15], $CAN_ADDRESS_HEX
      caninput_source_can_address1 = bits,   U16,     19,         [0:15], $CAN_ADDRESS_HEX
      caninput_source_can_address2 = bits,   U16,     21,         [0:15], $CAN_ADDRESS_HEX
      caninput_source_can_address3 = bits,   U16,     23,         [0:15], $CAN_ADDRESS_HEX
      caninput_source_can_address4 = bits,   U16,     25,         [0:15], $CAN_ADDRESS_HEX
      caninput_source_can_address5 = bits,   U16,     27,         [0:15], $CAN_ADDRESS_HEX
      caninput_source_can_address6 = bits,   U16,     29,         [0:15], $CAN_ADDRESS_HEX
      caninput_source_can_address7 = bits,   U16,     31,         [0:15], $CAN_ADDRESS_HEX
      caninput_source_can_address8 = bits,   U16,     33,         [0:15], $CAN_ADDRESS_HEX
      caninput_source_can_address9 = bits,   U16,     35,         [0:15], $CAN_ADDRESS_HEX
      caninput_source_can_address10 = bits,  U16,     37,         [0:15], $CAN_ADDRESS_HEX
      caninput_source_can_address11 = bits,  U16,     39,         [0:15], $CAN_ADDRESS_HEX
      caninput_source_can_address12 = bits,  U16,     41,         [0:15], $CAN_ADDRESS_HEX
      caninput_source_can_address13 = bits,  U16,     43,         [0:15], $CAN_ADDRESS_HEX
      caninput_source_can_address14 = bits,  U16,     45,         [0:15], $CAN_ADDRESS_HEX
      caninput_source_can_address15 = bits,  U16,     47,         [0:15], $CAN_ADDRESS_HEX

      caninput_source_start_byte0 = scalar, U08,     49,  "",       1, 0, 0, 7, 0
      caninput_source_start_byte1 = scalar, U08,     50,  "",       1, 0, 0, 7, 0
      caninput_source_start_byte2 = scalar, U08,     51,  "",       1, 0, 0, 7, 0
      caninput_source_start_byte3 = scalar, U08,     52,  "",       1, 0, 0, 7, 0
      caninput_source_start_byte4 = scalar, U08,     53,  "",       1, 0, 0, 7, 0
      caninput_source_start_byte5 = scalar, U08,     54,  "",       1, 0, 0, 7, 0
      caninput_source_start_byte6 = scalar, U08,     55,  "",       1, 0, 0, 7, 0
      caninput_source_start_byte7 = scalar, U08,     56,  "",       1, 0, 0, 7, 0
      caninput_source_start_byte8 = scalar, U08,     57,  "",       1, 0, 0, 7, 0
      caninput_source_start_byte9 = scalar, U08,     58,  "",       1, 0, 0, 7, 0
      caninput_source_start_byte10 = scalar, U08,     59,  "",       1, 0, 0, 7, 0
      caninput_source_start_byte11 = scalar, U08,     60,  "",       1, 0, 0, 7, 0
      caninput_source_start_byte12 = scalar, U08,     61,  "",       1, 0, 0, 7, 0
      caninput_source_start_byte13 = scalar, U08,     62,  "",       1, 0, 0, 7, 0
      caninput_source_start_byte14 = scalar, U08,     63,  "",       1, 0, 0, 7, 0
      caninput_source_start_byte15 = scalar, U08,     64,  "",       1, 0, 0, 7, 0

      caninput_source_num_bytes0 = bits,    U16,     65, [0:0], "1", "2"
      caninput_source_num_bytes1 = bits,    U16,     65, [1:1], "1", "2"
      caninput_source_num_bytes2 = bits,    U16,     65, [2:2], "1", "2"
      caninput_source_num_bytes3 = bits,    U16,     65, [3:3], "1", "2"
      caninput_source_num_bytes4 = bits,    U16,     65, [4:4], "1", "2"
      caninput_source_num_bytes5 = bits,    U16,     65, [5:5], "1", "2"
      caninput_source_num_bytes6 = bits,    U16,     65, [6:6], "1", "2"
      caninput_source_num_bytes7 = bits,    U16,     65, [7:7], "1", "2"
      caninput_source_num_bytes8 = bits,    U16,     65, [8:8], "1", "2"
      caninput_source_num_bytes9 = bits,    U16,     65, [9:9], "1", "2"
      caninput_source_num_bytes10 = bits,   U16,     65, [10:10], "1", "2"
      caninput_source_num_bytes11 = bits,   U16,     65, [11:11], "1", "2"
      caninput_source_num_bytes12 = bits,   U16,     65, [12:12], "1", "2"
      caninput_source_num_bytes13 = bits,   U16,     65, [13:13], "1", "2"
      caninput_source_num_bytes14 = bits,   U16,     65, [14:14], "1", "2"
      caninput_source_num_bytes15 = bits,   U16,     65, [15:15], "1", "2"      
      caninputEndianess           = bits,   U08,     67, [0:0], "Big-Endian", "Little-Endian"      
     
      unused10_68         = scalar, U08,     68,        "",       1, 0, 0, 255, 0
  
      enable_intcandata_out  = bits,   U08,     69, [0:0], "Off", "On"
      canoutput_sel0       = bits,   U08,    70, [0:0], "Off", "On"
      canoutput_sel1       = bits,   U08,    71, [0:0], "Off", "On"
      canoutput_sel2       = bits,   U08,    72, [0:0], "Off", "On"
      canoutput_sel3       = bits,   U08,    73, [0:0], "Off", "On"
      canoutput_sel4       = bits,   U08,    74, [0:0], "Off", "On"
      canoutput_sel5       = bits,   U08,    75, [0:0], "Off", "On"
      canoutput_sel6       = bits,   U08,    76, [0:0], "Off", "On"
      canoutput_sel7       = bits,   U08,    77, [0:0], "Off", "On"
      canoutput_param_group  = array ,  U16,   78,      [  8],  "",    1, 0, 0, 65535, 0
      canoutput_param_start_byte0 = bits,   U08,     94, [0:2], "0", "1", "2", "3", "4", "5", "6", "7"
      canoutput_param_start_byte1 = bits,   U08,     95, [0:2], "0", "1", "2", "3", "4", "5", "6", "7"
      canoutput_param_start_byte2 = bits,   U08,     96, [0:2], "0", "1", "2", "3", "4", "5", "6", "7"
      canoutput_param_start_byte3 = bits,   U08,     97, [0:2], "0", "1", "2", "3", "4", "5", "6", "7"
      canoutput_param_start_byte4 = bits,   U08,     98, [0:2], "0", "1", "2", "3", "4", "5", "6", "7"
      canoutput_param_start_byte5 = bits,   U08,     99, [0:2], "0", "1", "2", "3", "4", "5", "6", "7"
      canoutput_param_start_byte6 = bits,   U08,     100, [0:2], "0", "1", "2", "3", "4", "5", "6", "7"
      canoutput_param_start_byte7 = bits,   U08,     101, [0:2], "0", "1", "2", "3", "4", "5", "6", "7"
      canoutput_param_num_bytes0 = bits,   U08,     102, [0:1], "INVALID", "1", "2", "INVALID"
      canoutput_param_num_bytes1 = bits,   U08,     103, [0:1], "INVALID", "1", "2", "INVALID"
      canoutput_param_num_bytes2 = bits,   U08,     104, [0:1], "INVALID", "1", "2", "INVALID"
      canoutput_param_num_bytes3 = bits,   U08,     105, [0:1], "INVALID", "1", "2", "INVALID"
      canoutput_param_num_bytes4 = bits,   U08,     106, [0:1], "INVALID", "1", "2", "INVALID"
      canoutput_param_num_bytes5 = bits,   U08,     107, [0:1], "INVALID", "1", "2", "INVALID"
      canoutput_param_num_bytes6 = bits,   U08,     108, [0:1], "INVALID", "1", "2", "INVALID"
      canoutput_param_num_bytes7 = bits,   U08,     109, [0:1], "INVALID", "1", "2", "INVALID"
      
      unused10_110         = scalar, U08,     110,        "",       1, 0, 0, 255, 0 
      unused10_111         = scalar, U08,     111,        "",       1, 0, 0, 255, 0
      egoMAPMax = scalar, U08, 112, "kPa", 2.0, 0.0, 2.0, 511.0, 0
      egoMAPMin = scalar, U08, 113, "kPa", 2.0, 0.0, 2.0, 511.0, 0

      speeduino_tsCanId     = bits,   U08,    114,     [0:3],  $tsCanId_list
      true_address           = bits,   U16,     115,     [0:15], $CAN_ADDRESS_HEX
      realtime_base_address  = bits,   U16,     117,     [0:15], $CAN_ADDRESS_HEX
      obd_address            = bits,   U16,     119,       [0:15], $CAN_ADDRESS_HEX

#if mcu_teensy
      Auxin0pina        = bits,   U08,    121,     [0:5],  $ANALOG_PIN_TEENSY
      Auxin1pina        = bits,   U08,    122,     [0:5],  $ANALOG_PIN_TEENSY
      Auxin2pina        = bits,   U08,    123,     [0:5],  $ANALOG_PIN_TEENSY
      Auxin3pina        = bits,   U08,    124,     [0:5],  $ANALOG_PIN_TEENSY
      Auxin4pina        = bits,   U08,    125,     [0:5],  $ANALOG_PIN_TEENSY
      Auxin5pina        = bits,   U08,    126,     [0:5],  $ANALOG_PIN_TEENSY
      Auxin6pina        = bits,   U08,    127,     [0:5],  $ANALOG_PIN_TEENSY
      Auxin7pina        = bits,   U08,    128,     [0:5],  $ANALOG_PIN_TEENSY
      Auxin8pina        = bits,   U08,    129,     [0:5],  $ANALOG_PIN_TEENSY
      Auxin9pina        = bits,   U08,    130,     [0:5],  $ANALOG_PIN_TEENSY
      Auxin10pina       = bits,   U08,    131,     [0:5],  $ANALOG_PIN_TEENSY
      Auxin11pina       = bits,   U08,    132,     [0:5],  $ANALOG_PIN_TEENSY
      Auxin12pina       = bits,   U08,    133,     [0:5],  $ANALOG_PIN_TEENSY
      Auxin13pina       = bits,   U08,    134,     [0:5],  $ANALOG_PIN_TEENSY
      Auxin14pina       = bits,   U08,    135,     [0:5],  $ANALOG_PIN_TEENSY
      Auxin15pina       = bits,   U08,    136,     [0:5],  $ANALOG_PIN_TEENSY

      Auxin0pinb        = bits,   U08,    137,     [0:5],  $DIGITAL_AUX_PIN_TEENSY
      Auxin1pinb        = bits,   U08,    138,     [0:5],  $DIGITAL_AUX_PIN_TEENSY
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
      Auxin7pina        = bits,   U08,    128,     [0:5],  $ANALOG_PIN_MEGA
      Auxin8pina        = bits,   U08,    129,     [0:5],  $ANALOG_PIN_MEGA
      Auxin9pina        = bits,   U08,    130,     [0:5],  $ANALOG_PIN_MEGA
      Auxin10pina       = bits,   U08,    131,     [0:5],  $ANALOG_PIN_MEGA
      Auxin11pina       = bits,   U08,    132,     [0:5],  $ANALOG_PIN_MEGA
      Auxin12pina       = bits,   U08,    133,     [0:5],  $ANALOG_PIN_MEGA
      Auxin13pina       = bits,   U08,    134,     [0:5],  $ANALOG_PIN_MEGA
      Auxin14pina       = bits,   U08,    135,     [0:5],  $ANALOG_PIN_MEGA
      Auxin15pina       = bits,   U08,    136,     [0:5],  $ANALOG_PIN_MEGA

      Auxin0pinb        = bits,   U08,    137,     [0:5],  $DIGITAL_AUX_PIN_MEGA
      Auxin1pinb        = bits,   U08,    138,     [0:5],  $DIGITAL_AUX_PIN_MEGA
      Auxin2pinb        = bits,   U08,    139,     [0:5],  $DIGITAL_AUX_PIN_MEGA
      Auxin3pinb        = bits,   U08,    140,     [0:5],  $DIGITAL_AUX_PIN_MEGA
      Auxin4pinb        = bits,   U08,    141,     [0:5],  $DIGITAL_AUX_PIN_MEGA
      Auxin5pinb        = bits,   U08,    142,     [0:5],  $DIGITAL_AUX_PIN_MEGA
      Auxin6pinb        = bits,   U08,    143,     [0:5],  $DIGITAL_AUX_PIN_MEGA
      Auxin7pinb        = bits,   U08,    144,     [0:5],  $DIGITAL_AUX_PIN_MEGA
      Auxin8pinb        = bits,   U08,    145,     [0:5],  $DIGITAL_AUX_PIN_MEGA
      Auxin9pinb        = bits,   U08,    146,     [0:5],  $DIGITAL_AUX_PIN_MEGA
      Auxin10pinb       = bits,   U08,    147,     [0:5],  $DIGITAL_AUX_PIN_MEGA
      Auxin11pinb       = bits,   U08,    148,     [0:5],  $DIGITAL_AUX_PIN_MEGA
      Auxin12pinb       = bits,   U08,    149,     [0:5],  $DIGITAL_AUX_PIN_MEGA
      Auxin13pinb       = bits,   U08,    150,     [0:5],  $DIGITAL_AUX_PIN_MEGA
      Auxin14pinb       = bits,   U08,    151,     [0:5],  $DIGITAL_AUX_PIN_MEGA
      Auxin15pinb       = bits,   U08,    152,     [0:5],  $DIGITAL_AUX_PIN_MEGA
#endif

      iacStepperInv       = bits,   U08,   153, [0:0], "No",        "Yes"
      iacCoolTime         = bits,   U08,   153, [1:3], "0", "1", "2", "3", "4", "5", "6","INVALID"

      boostByGearEnabled  = bits,   U08,   153, [4:5],      "Off", "Multiplied %", "Constant limit", "INVALID"

      blankfield          = bits,   U08,   153, [6:6], "",""
      iacStepperPower     = bits,   U08,   153, [7:7], "When Active", "Always"
      
      iacMaxSteps         = scalar, U08,     154,     "Steps",     3,    0,  0,  {iacStepHome-3},    0
      idleAdvStartDelay   = scalar, U08,     155,         "S",   0.1,  0.0,   0.0,    25.5,          1

      boostByGear1               = scalar, U08,     156, { bitStringValue(boostByGearLabels ,  boostByGearEnabled) },   2.0,   0.0,  0.0,  {boostTableLimit},      0
      boostByGear2               = scalar, U08,     157, { bitStringValue(boostByGearLabels ,  boostByGearEnabled) },   2.0,   0.0,  0.0,  {boostTableLimit},      0
      boostByGear3               = scalar, U08,     158, { bitStringValue(boostByGearLabels ,  boostByGearEnabled) },   2.0,   0.0,  0.0,  {boostTableLimit},      0
      boostByGear4               = scalar, U08,     159, { bitStringValue(boostByGearLabels ,  boostByGearEnabled) },   2.0,   0.0,  0.0,  {boostTableLimit},      0
      boostByGear5               = scalar, U08,     160, { bitStringValue(boostByGearLabels ,  boostByGearEnabled) },   2.0,   0.0,  0.0,  {boostTableLimit},      0
      boostByGear6               = scalar, U08,     161, { bitStringValue(boostByGearLabels ,  boostByGearEnabled) },   2.0,   0.0,  0.0,  {boostTableLimit},      0

      PWMFanDuty                 = array,  U08,     162, [4],       "%", 0.5,    0,    0,    100,      1

      hardRevMode       = bits,   U08,     166, [0:1], "Off", "Fixed", "Coolant based", "INVALID"      
      coolantProtRPM    = array,  U08,     167, [6], "RPM",     100.0,       0.0,   100.0, 25500,    0           
      #if CELSIUS
      coolantProtTemp   = array,  U08,      173, [6],    "C",    1.0,    -40,    -40,    215,      0
      #else
      coolantProtTemp   = array,  U08,      173, [6],    "F",    1.8, -22.23,    -40,    419,      0
      #endif

      unused10_179               = scalar, U08, 179,        "",       1, 0, 0, 255, 0 

      dfcoTaperTime              = scalar, U08, 180, "S",      0.1,  0.0,  0.0,  25.5,   1
      dfcoTaperFuel              = scalar, U08, 181, "%",      1.0,  0.0,    0,   255,   0
      dfcoTaperAdvance           = scalar, U08, 182, "deg",    1.0,  0.0,    0,    40,   0
      dfcoTaperEnable            = bits,   U08, 183, [0:0],   "Off", "On"
      unused10_182               = bits,   U08, 183, [1:7],     ""

      unused10_184               = scalar, U08, 184,        "",       1, 0, 0, 255, 0 

      ; AFR engine protection
      afrProtectEnabled         = bits, U08, 185, [0:1], "Off", "Fixed mode", "Table mode", "INVALID"
      afrProtectMAP             = scalar, U08, 186, "kPa", 2.0, 0.0, 0.0, 511.0, 0      ; 8 bit value, 1 byte
      afrProtectRPM             = scalar, U08, 187, "RPM", 100, 0.0, 100, 25500, 0      ; 8 bit value, 1 byte
      afrProtectTPS             = scalar, U08, 188, "%", 0.5, 0.0, 0.0, 100.0, 1     ; 8 bit value, 1 byte
      afrProtectDeviationLambda = scalar, U08, 189, "Lambda", {0.1 / stoich}, 0.0, 0.00, 25.5, 3    ; 8 bit value, 1 byte
      afrProtectDeviation       = scalar, U08, lastOffset, "AFR", 0.1, 0.0, 0.0, 25.5, 1       ; 8 bit value, 1 byte
      afrProtectCutTime         = scalar, U08, 190, "seconds", 0.1, 0.0, 0.0, 2.5, 1        ; 8 bit value, 1 byte
      afrProtectReactivationTPS = scalar, U08, 191, "%", 0.5, 0.0, 0.0, 100.0, 1     ; 8 bit value, 1 byte
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
